khartinger/RCC5V_3d-printable-parts-for-n-scale-modules/images/300_3D_blockpanel_2of3.png

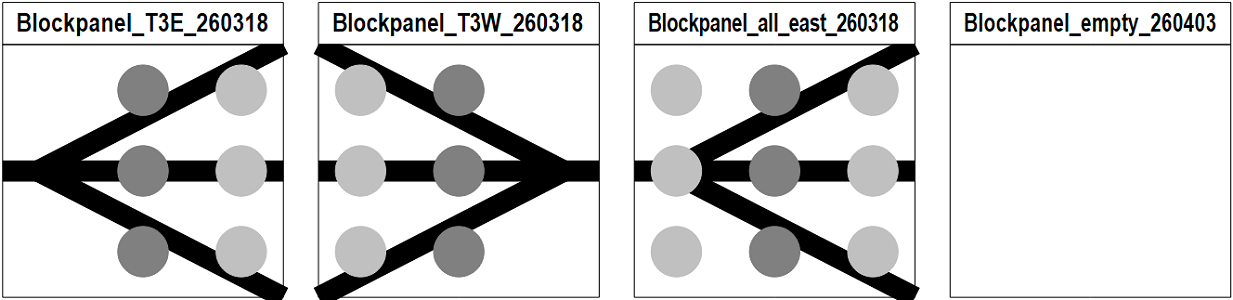
images/300_3D_blockpanel_2of3.png
