khartinger/RCC5V_3d-printable-parts-for-n-scale-modules/images/300_bahnkoerper2.png

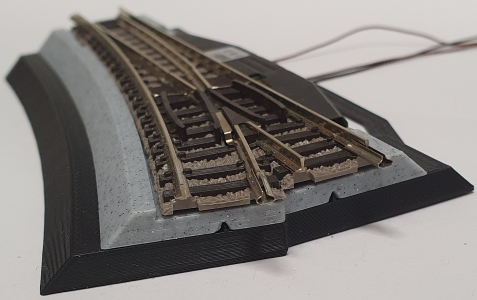
images/300_bahnkoerper2.png
