khartinger/RCC5V_3d-printable-parts-for-n-scale-modules/images/300_pp6_point_motor_cover_t2r_stairs_in.png

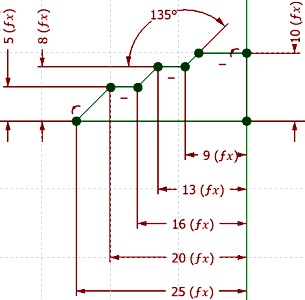
images/300_pp6_point_motor_cover_t2r_stairs_in.png
