khartinger/RCC5V_3d-printable-parts-for-n-scale-modules/images/o_3D_blockpanel_3of3.png

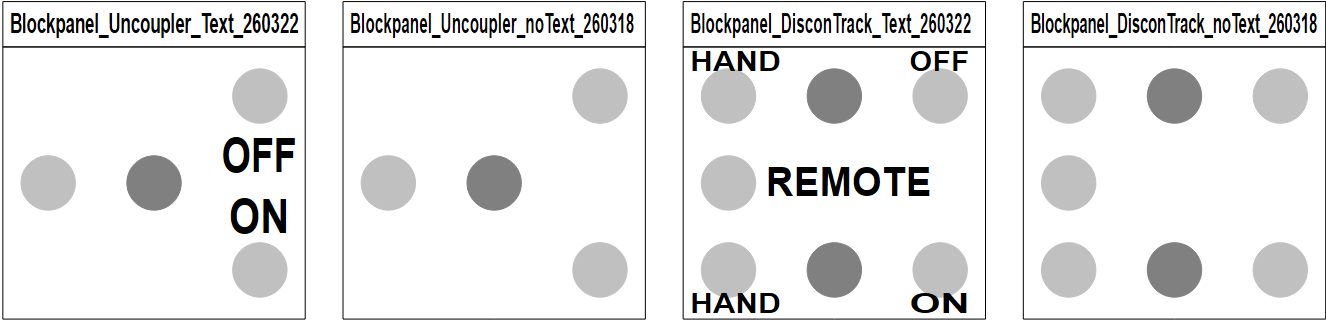
images/o_3D_blockpanel_3of3.png
