khartinger/RCC5V_3d-printable-parts-for-n-scale-modules/fab/pp2_baseboard_frame/3mf/Rahmen_2xFront_S__230mm_260408.3mf

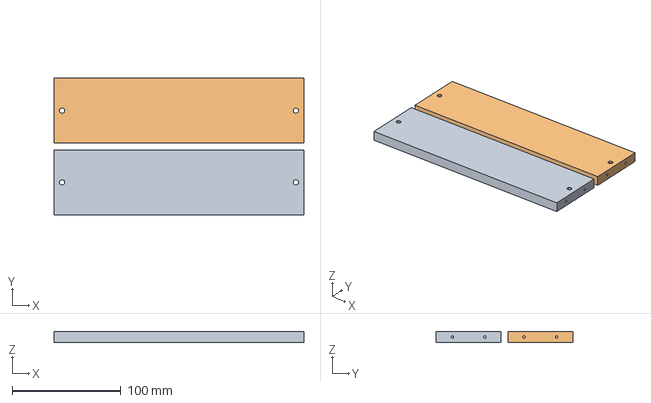
[picture p55: CAD file, 2026-04-10]
fab/pp2_baseboard_frame/3mf/Rahmen_2xFront_S__230mm_260408.3mf
230.0 x 126.0 x 10.0 mm
Rahmen_Front_S__230mm_260408 x 2
