khartinger/RCC5V_3d-printable-parts-for-n-scale-modules/fab/pp2_baseboard_frame/fcstd/Rahmen_Front_S__230mm_260408.FCStd

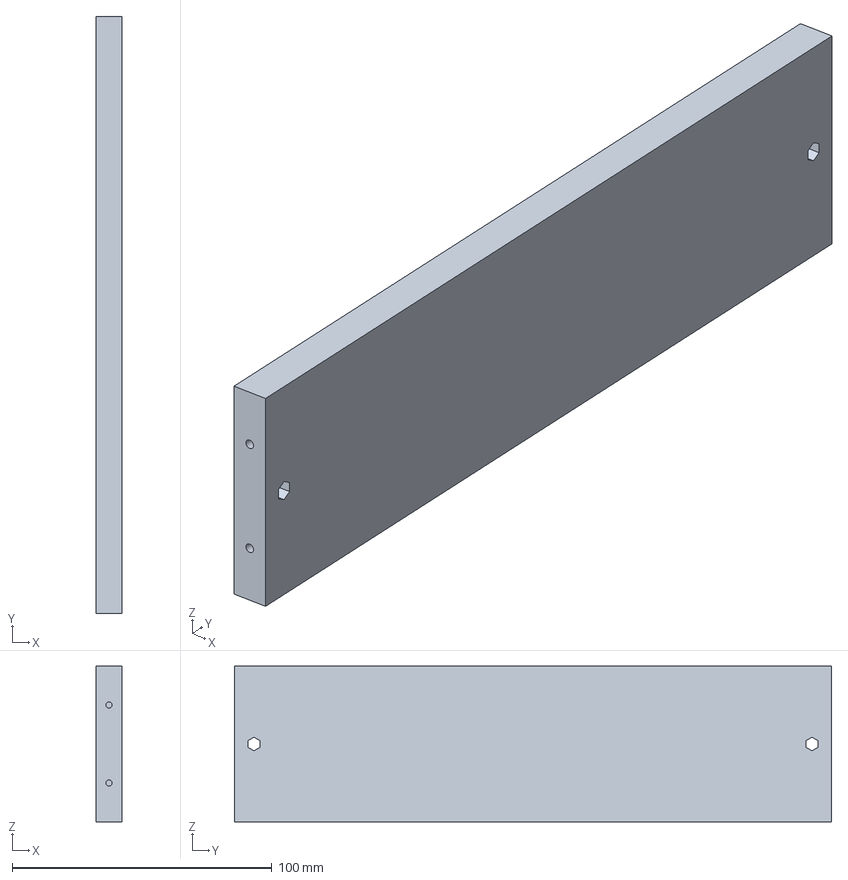
[picture p56: CAD file, 2026-04-10]
fab/pp2_baseboard_frame/fcstd/Rahmen_Front_S__230mm_260408.FCStd
10.0 x 230.0 x 60.0 mm
