khartinger/RCC5V_3d-printable-parts-for-n-scale-modules/fab/pp3_block_panel/3mf/Blockpanel_empty_prusa_260403.3mf

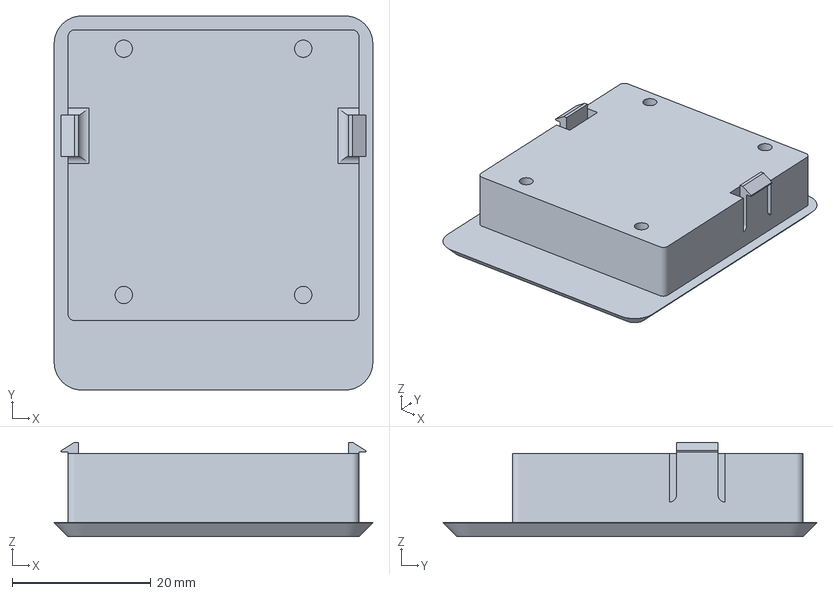
[picture p57: CAD file, 2026-04-10]
fab/pp3_block_panel/3mf/Blockpanel_empty_prusa_260403.3mf
46.0 x 54.0 x 13.6 mm
