khartinger/RCC5V_3d-printable-parts-for-n-scale-modules/fab/pp3_block_panel/fcstd/Blockpanel_DisconTrack_Text_260322.FCStd

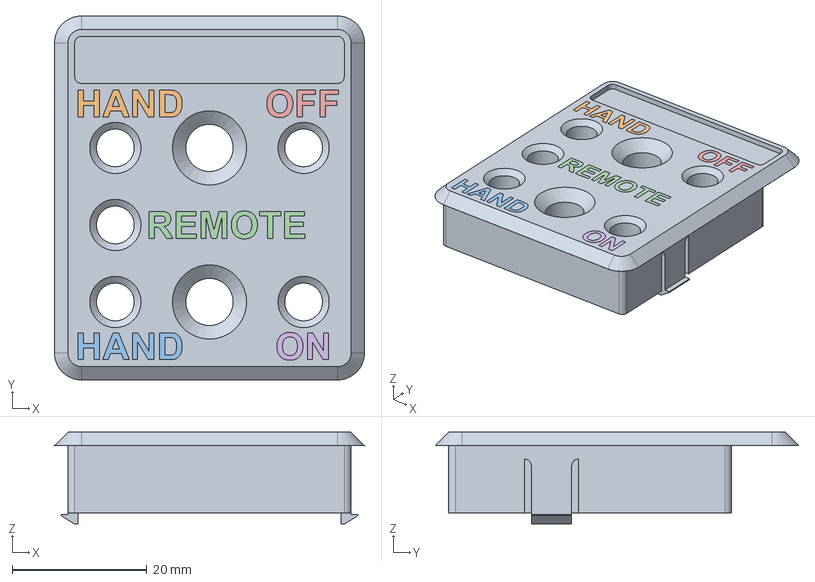
[picture p59: CAD file, 2026-04-05]
fab/pp3_block_panel/fcstd/Blockpanel_DisconTrack_Text_260322.FCStd
46.0 x 54.0 x 13.6 mm
KörperBlock
Extrude_HAND1
Extrude_HAND2
Extrude_REM
Extrude_OFF
Extrude_ON
