khartinger/RCC5V_3d-printable-parts-for-n-scale-modules/fab/pp4_track_ballast/fcstd/Bogen_Schotter_R2_7.5_9128_260327.FCStd

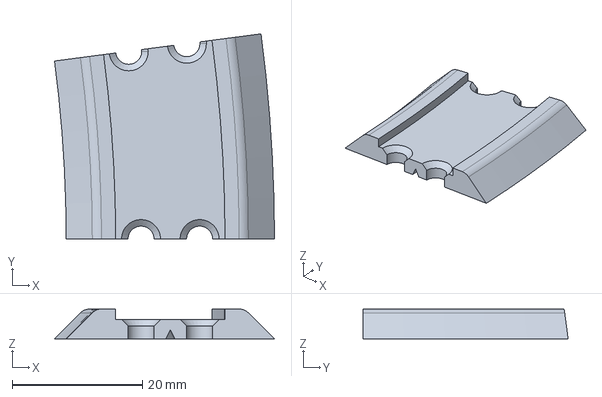
[picture p60: CAD file, 2026-04-17]
fab/pp4_track_ballast/fcstd/Bogen_Schotter_R2_7.5_9128_260327.FCStd
33.8 x 31.5 x 4.60 mm
