khartinger/RCC5V_3d-printable-parts-for-n-scale-modules/fab/pp6_point_motor_cover/fcstd/point_motor_cover_t3r_high_260413.FCStd

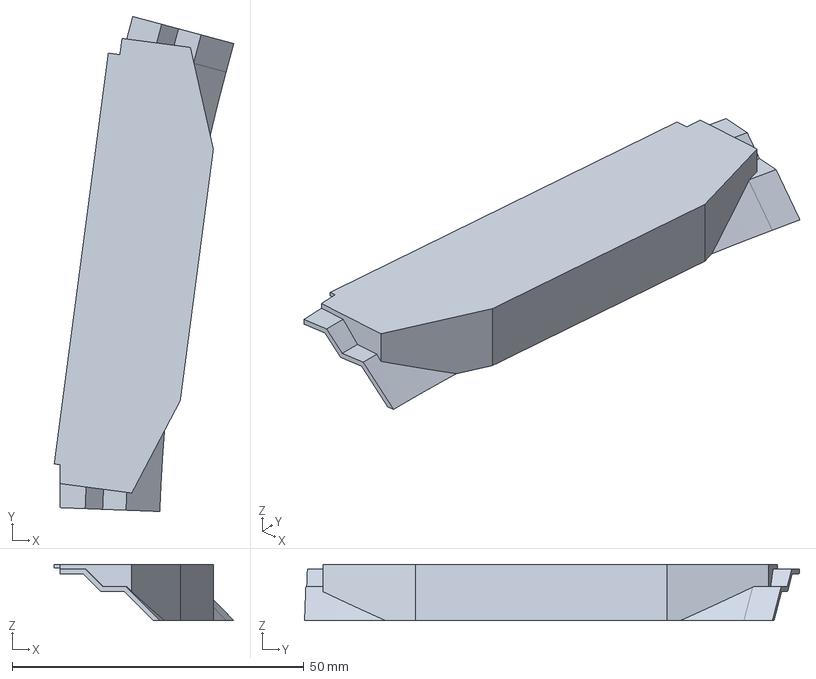
[picture p61: CAD file, 2026-04-13]
fab/pp6_point_motor_cover/fcstd/point_motor_cover_t3r_high_260413.FCStd
30.8 x 84.8 x 9.60 mm
