khartinger/RCC5V_3d-printable-parts-for-n-scale-modules/fab/pp7_tools/fcstd/drill_template_T2_260413.FCStd

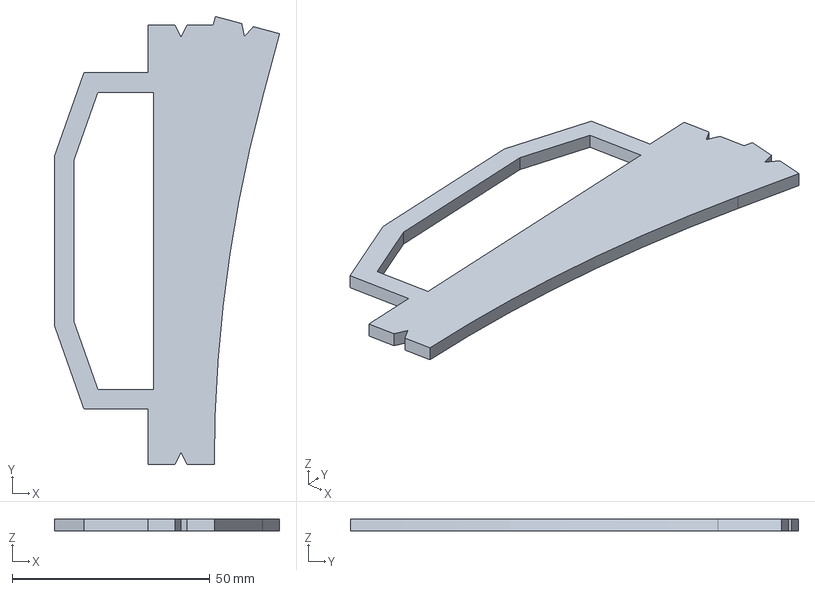
[picture p62: CAD file, 2026-04-13]
fab/pp7_tools/fcstd/drill_template_T2_260413.FCStd
56.9 x 113.2 x 3.00 mm
