khartinger/RCC5V_3d-printable-parts-for-n-scale-modules/fab/pp7_tools/raaco_lid/3mf/Raacodeckel_A9-2_5x_PETG_260427.3mf

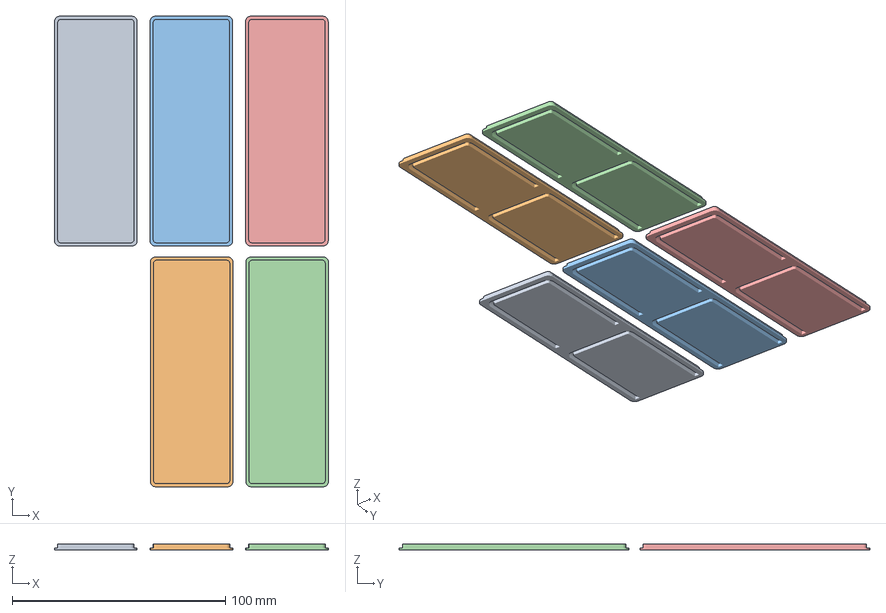
[picture p63: CAD file, 2026-04-29]
fab/pp7_tools/raaco_lid/3mf/Raacodeckel_A9-2_5x_PETG_260427.3mf
128.5 x 220.7 x 3.00 mm
Raacodeckel_A9-2_c_260414 x 5
