khartinger/RCC5V_3d-printable-parts-for-n-scale-modules/fab/pp7_tools/raaco_lid/fcstd/Raacodeckel_A8-1_260415.FCStd

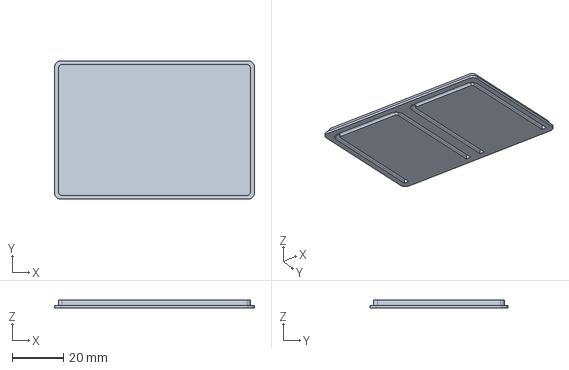
[picture p64: CAD file, 2026-04-15]
fab/pp7_tools/raaco_lid/fcstd/Raacodeckel_A8-1_260415.FCStd
78.0 x 54.0 x 3.00 mm
