khartinger/RCC5V_3d-printable-parts-for-n-scale-modules/fab/pp8_supplement/3mf/suppl_strightcurvedR3_E8_15deg_260429.3mf

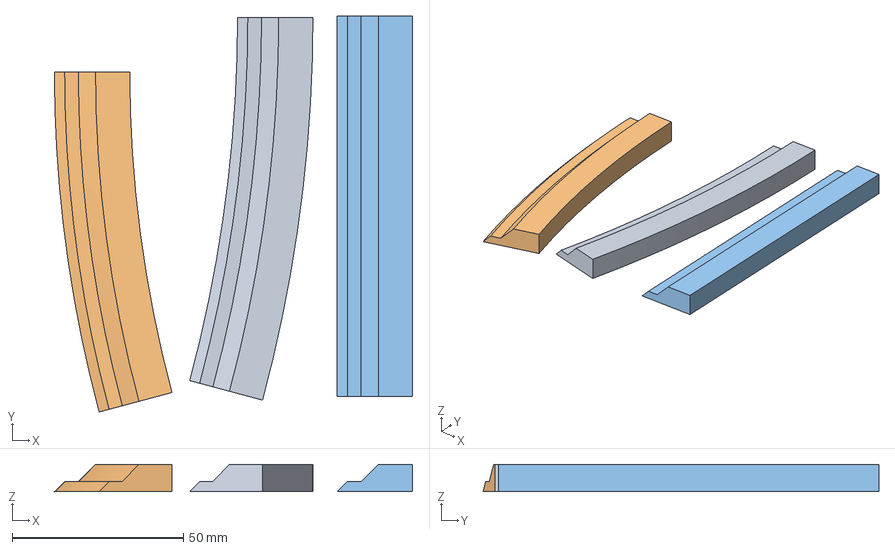
[picture p65: CAD file, 2026-04-30]
fab/pp8_supplement/3mf/suppl_strightcurvedR3_E8_15deg_260429.3mf
104.5 x 115.5 x 8.00 mm
suppl_curvedR3out_E8_15deg_260429
suppl_curvedR3in_E8_15deg_260429
suppl_straight_E8_111mm_260429
