khartinger/RCC5V_3d-printable-parts-for-n-scale-modules/fab/pp9_projects/ReflectiveOptocoupler/3mf/Opto_Beilage_alle_260531.3mf

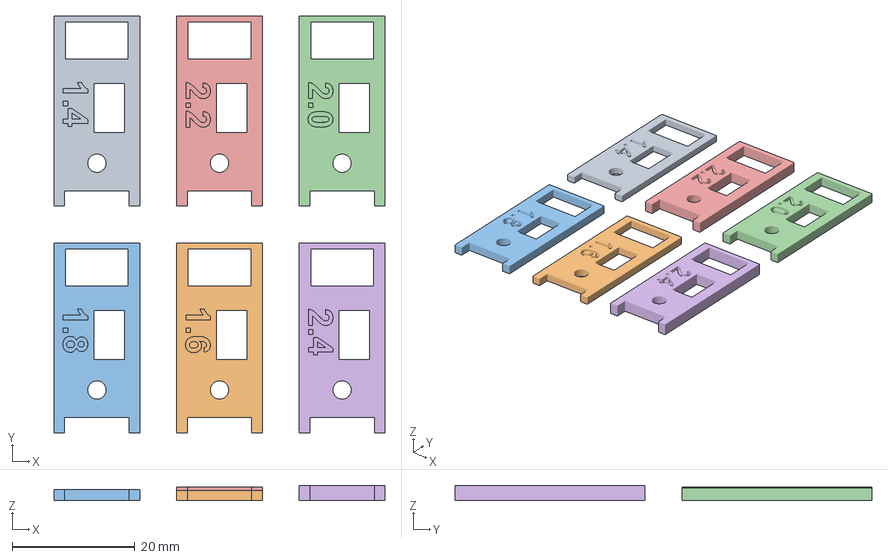
[picture p67: CAD file, 2026-06-02]
fab/pp9_projects/ReflectiveOptocoupler/3mf/Opto_Beilage_alle_260531.3mf
54.0 x 68.0 x 2.40 mm
Opto_Beilage_1.4mm_260531
Opto_Beilage_1.6mm_260531
Opto_Beilage_1.8mm_260531
Opto_Beilage_2.0mm_260531
Opto_Beilage_2.2mm_260531
Opto_Beilage_2.4mm_260531
