khartinger/RCC5V_3d-printable-parts-for-n-scale-modules/fab/pp9_projects/ReflectiveOptocoupler/fcstd/Gerade_Schotter_9103_Opto_b_260531.FCStd

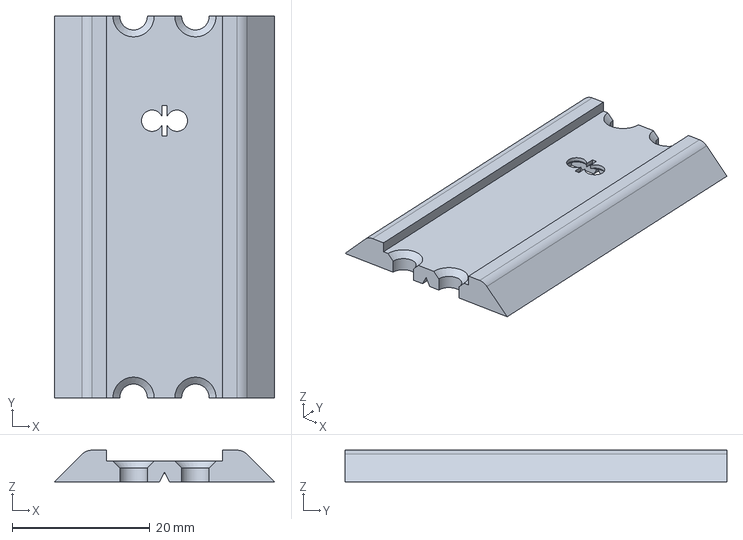
[picture p68: CAD file, 2026-06-02]
fab/pp9_projects/ReflectiveOptocoupler/fcstd/Gerade_Schotter_9103_Opto_b_260531.FCStd
32.0 x 55.5 x 4.60 mm
