khartinger/RCC5V_3d-printable-parts-for-n-scale-modules/fab/pp2_baseboard_frame/3mf/Rahmen_2xSeiteEingleisig_260312.3mf

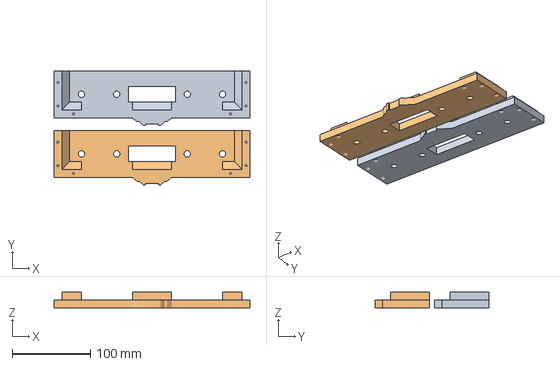
[picture p69: CAD file, 2026-04-10]
fab/pp2_baseboard_frame/3mf/Rahmen_2xSeiteEingleisig_260312.3mf
250.0 x 146.0 x 20.0 mm
Rahmen_SeiteEingleisig_260312 x 2
