khartinger/RCC5V_3d-printable-parts-for-n-scale-modules/fab/pp2_baseboard_frame/fcstd/Rahmen_SeiteEingleisig_260312.FCStd

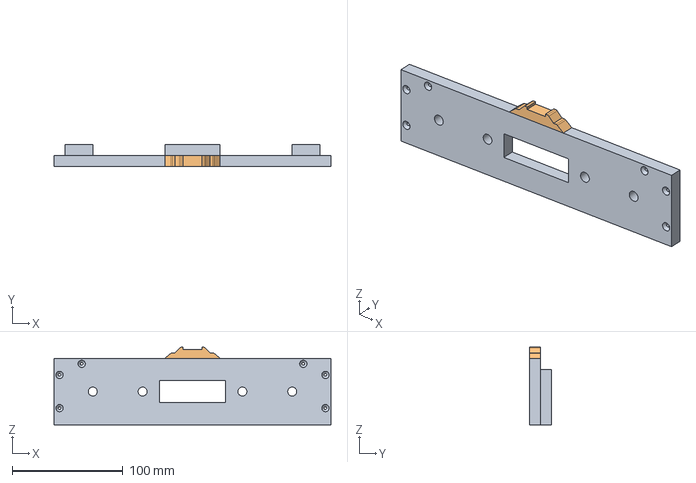
[picture p70: CAD file, 2026-04-06]
fab/pp2_baseboard_frame/fcstd/Rahmen_SeiteEingleisig_260312.FCStd
250.0 x 20.0 x 70.0 mm
KörperRahmen
Körper1Gleis
