khartinger/RCC5V_3d-printable-parts-for-n-scale-modules/fab/pp3_block_panel/3mf/Blockpanel_4x_empty_prusa_260404.3mf

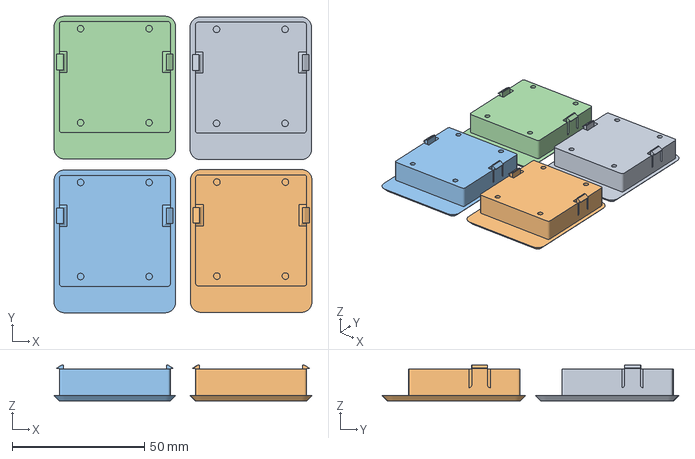
[picture p71: CAD file, 2026-04-10]
fab/pp3_block_panel/3mf/Blockpanel_4x_empty_prusa_260404.3mf
97.6 x 112.2 x 13.6 mm
Blockpanel_empty_260403 x 4
