khartinger/RCC5V_3d-printable-parts-for-n-scale-modules/fab/pp6_point_motor_cover/3mf/point_motor_cover_t2_E8_pair_260413.3mf

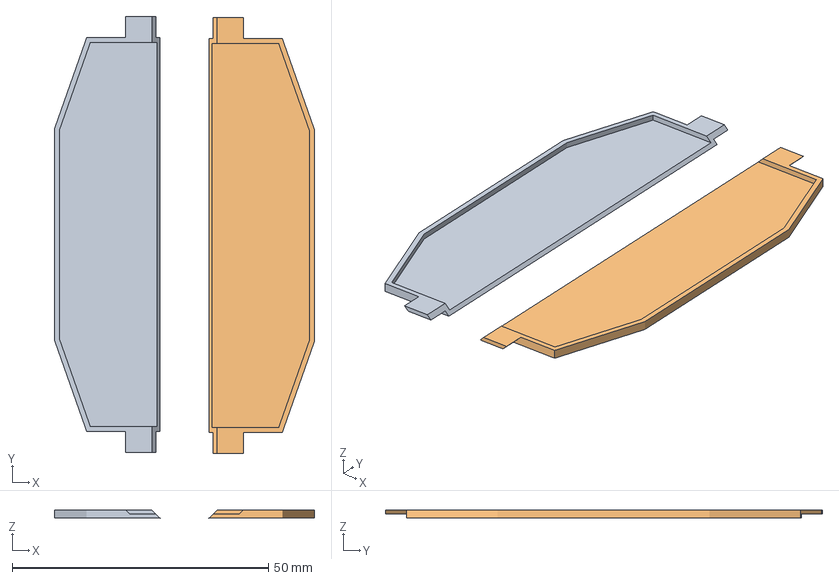
[picture p75: CAD file, 2026-04-13]
fab/pp6_point_motor_cover/3mf/point_motor_cover_t2_E8_pair_260413.3mf
50.8 x 85.4 x 1.60 mm
point_motor_cover_t2r_E8_260413 x 2
