khartinger/RCC5V_3d-printable-parts-for-n-scale-modules/fab/pp6_point_motor_cover/fcstd/point_motor_cover_t2r_E8_260413.FCStd

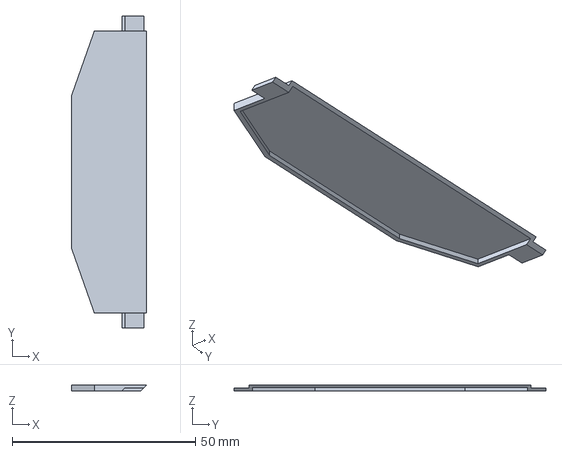
[picture p76: CAD file, 2026-04-13]
fab/pp6_point_motor_cover/fcstd/point_motor_cover_t2r_E8_260413.FCStd
20.6 x 85.2 x 1.60 mm
