khartinger/RCC5V_3d-printable-parts-for-n-scale-modules/fab/pp7_tools/fcstd/drill_template_T3_260413.FCStd

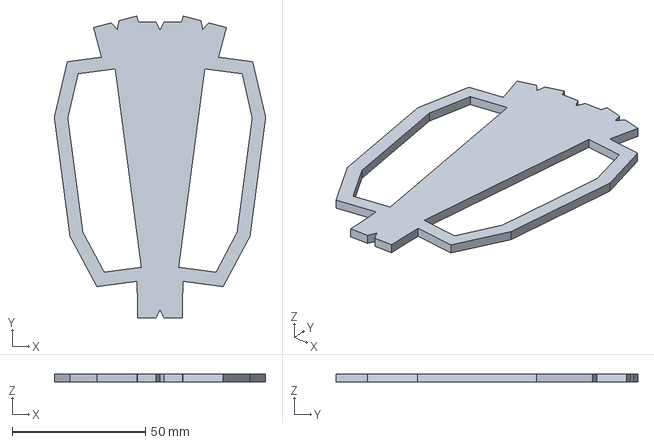
[picture p77: CAD file, 2026-04-13]
fab/pp7_tools/fcstd/drill_template_T3_260413.FCStd
79.2 x 113.2 x 3.00 mm
