khartinger/RCC5V_3d-printable-parts-for-n-scale-modules/fab/pp2_baseboard_frame/3mf/Rahmen_Front_W__240mm_prusa_260406.3mf

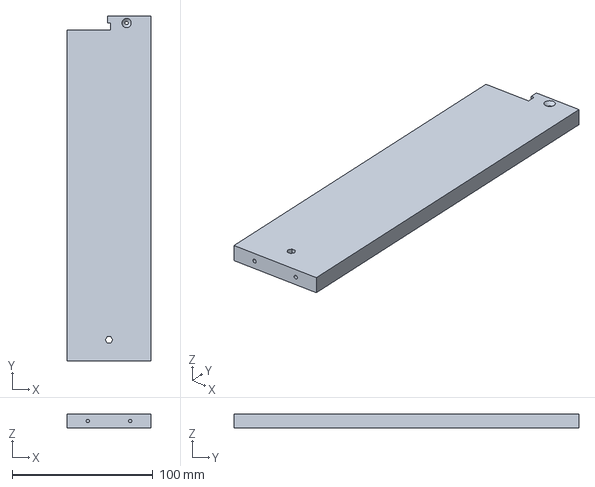
[picture p80: CAD file, 2026-04-06]
fab/pp2_baseboard_frame/3mf/Rahmen_Front_W__240mm_prusa_260406.3mf
60.0 x 245.0 x 10.0 mm
