khartinger/RCC5V_3d-printable-parts-for-n-scale-modules/fab/pp2_baseboard_frame/fcstd/Rahmen_Front_S__250mm_260406.FCStd

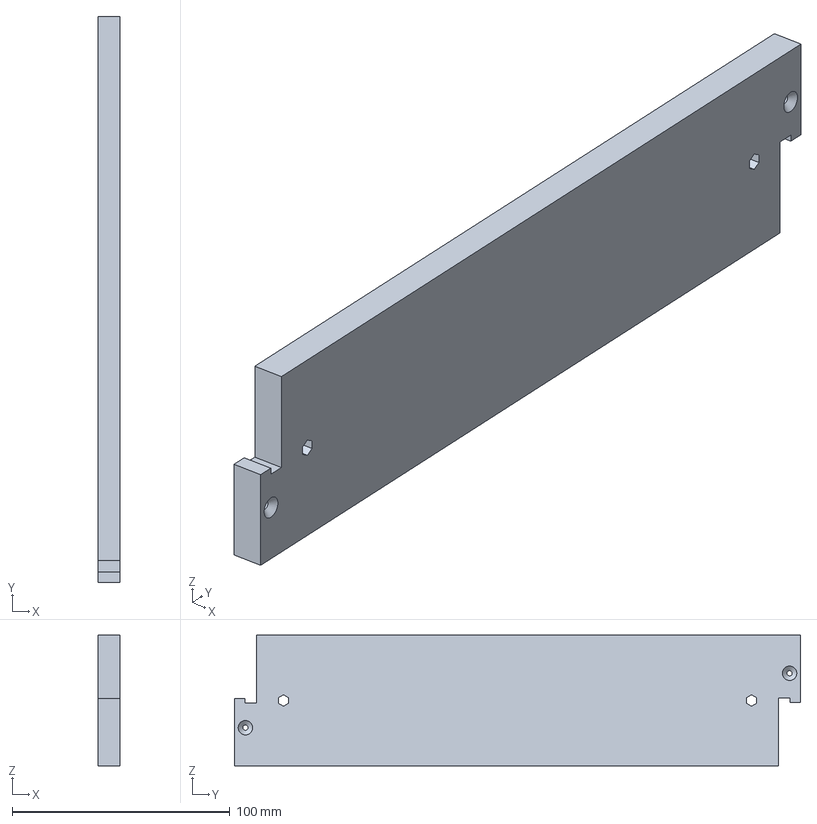
[picture p81: CAD file, 2026-04-06]
fab/pp2_baseboard_frame/fcstd/Rahmen_Front_S__250mm_260406.FCStd
10.0 x 260.0 x 60.0 mm
