khartinger/RCC5V_3d-printable-parts-for-n-scale-modules/fab/pp3_block_panel/3mf/Block_alles_260314.3mf

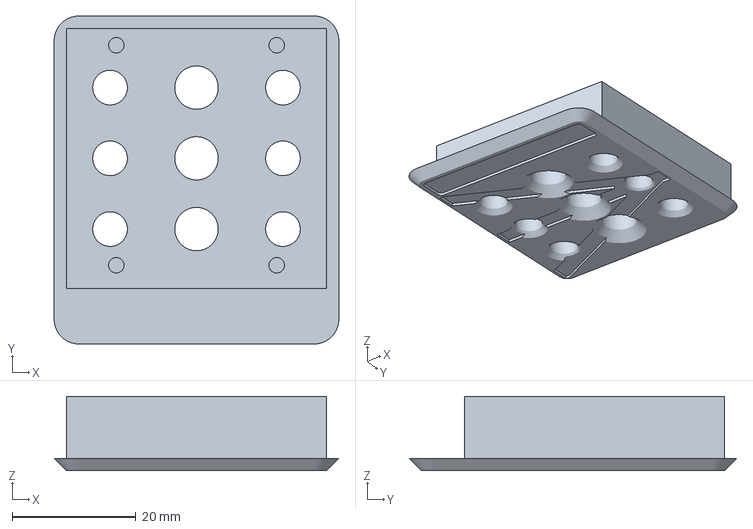
[picture p82: CAD file, 2026-04-10]
fab/pp3_block_panel/3mf/Block_alles_260314.3mf
46.0 x 53.0 x 12.0 mm
