khartinger/RCC5V_3d-printable-parts-for-n-scale-modules/fab/pp4_track_ballast/fcstd/Gerade_Schotter_9101_-10mm_260403.FCStd

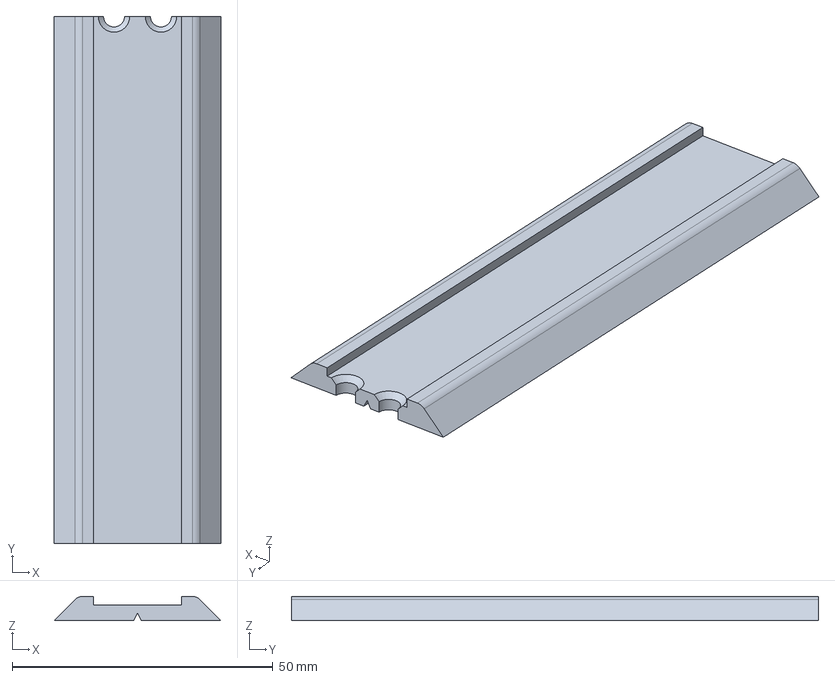
[picture p84: CAD file, 2026-04-17]
fab/pp4_track_ballast/fcstd/Gerade_Schotter_9101_-10mm_260403.FCStd
32.0 x 101.0 x 4.60 mm
