khartinger/RCC5V_3d-printable-parts-for-n-scale-modules/fab/pp5_embankment/fcstd/Gerade_Damm_9100_260429.FCStd

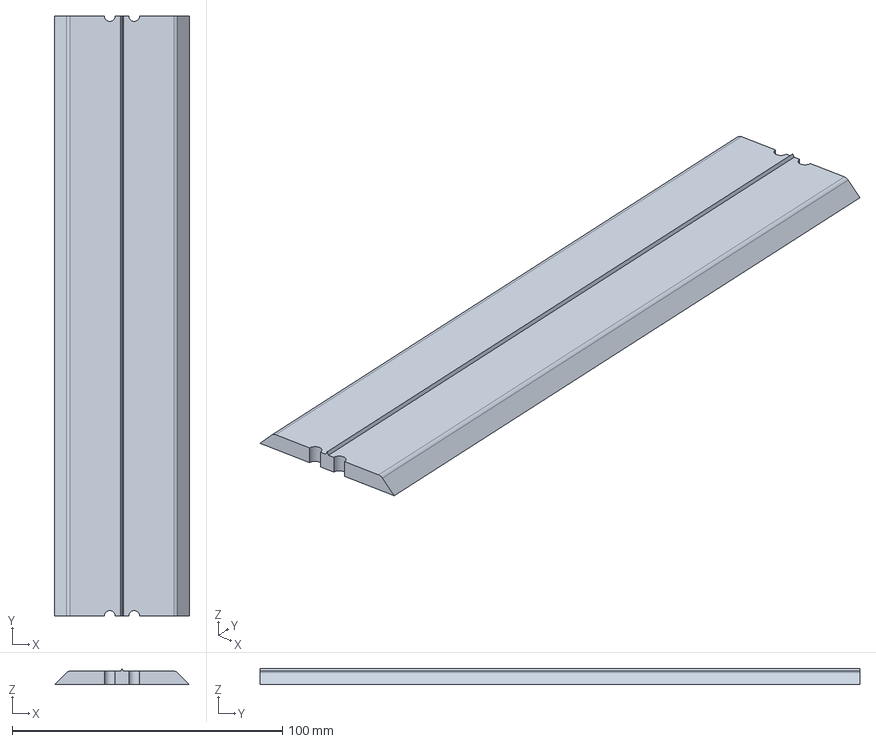
[picture p85: CAD file, 2026-04-29]
fab/pp5_embankment/fcstd/Gerade_Damm_9100_260429.FCStd
50.0 x 222.0 x 6.00 mm
