khartinger/RCC5V_3d-printable-parts-for-n-scale-modules/fab/pp6_point_motor_cover/3mf/point_motor_cover_t3_E8_pair_260413.3mf

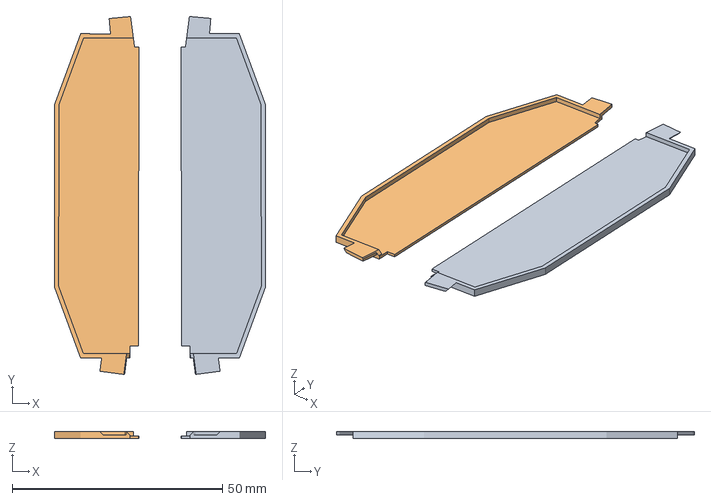
[picture p86: CAD file, 2026-04-13]
fab/pp6_point_motor_cover/3mf/point_motor_cover_t3_E8_pair_260413.3mf
50.1 x 85.1 x 1.60 mm
point_motor_cover_t3r_E8_260413 x 2
