khartinger/RCC5V_3d-printable-parts-for-n-scale-modules/fab/pp6_point_motor_cover/fcstd/point_motor_cover_t2r_high_260413.FCStd

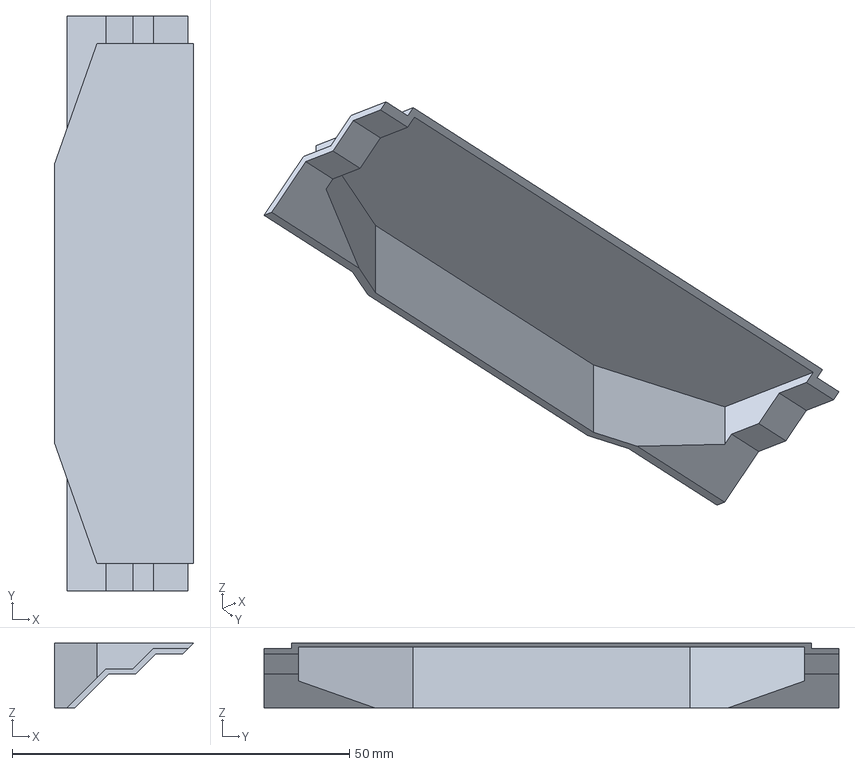
[picture p87: CAD file, 2026-04-13]
fab/pp6_point_motor_cover/fcstd/point_motor_cover_t2r_high_260413.FCStd
20.6 x 85.2 x 9.60 mm
