khartinger/RCC5V_3d-printable-parts-for-n-scale-modules/fab/pp8_supplement/fcstd/suppl_curvedR3out_E8_15deg_260429.FCStd

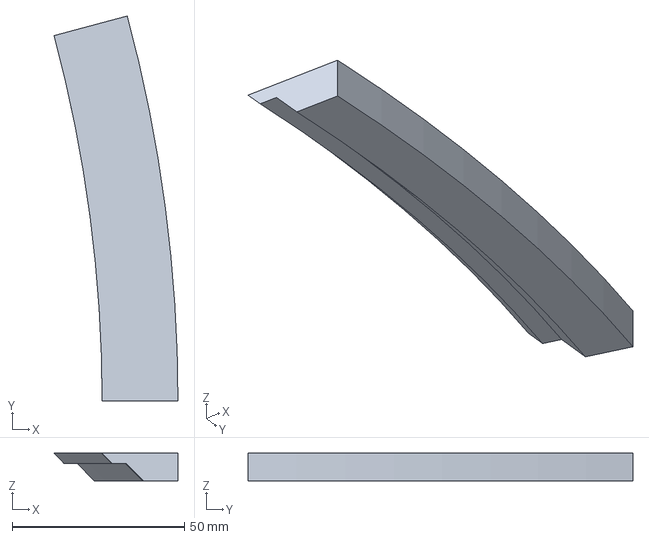
[picture p88: CAD file, 2026-04-30]
fab/pp8_supplement/fcstd/suppl_curvedR3out_E8_15deg_260429.FCStd
35.9 x 111.7 x 8.00 mm
