khartinger/RCC5V_3d-printable-parts-for-n-scale-modules/fab/pp9_projects/ReflectiveOptocoupler/fcstd/Optobohrlehre_9103_260527.FCStd

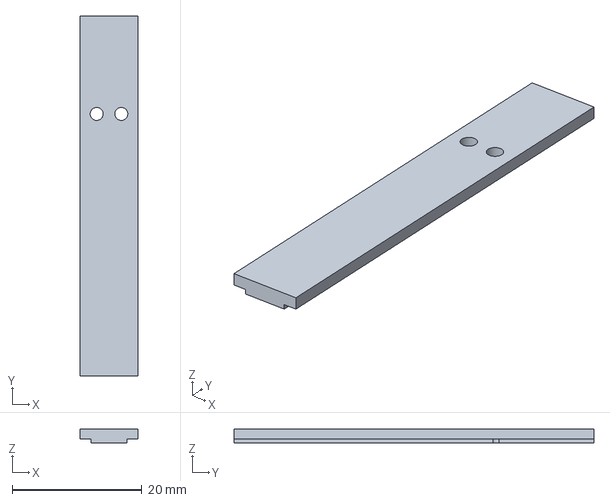
[picture p89: CAD file, 2026-06-02]
fab/pp9_projects/ReflectiveOptocoupler/fcstd/Optobohrlehre_9103_260527.FCStd
9.00 x 55.5 x 2.10 mm
