khartinger/RCC5V_3d-printable-parts-for-n-scale-modules/fab/pp4_track_ballast/fcstd/Weiche3_Schotter_260409.FCStd

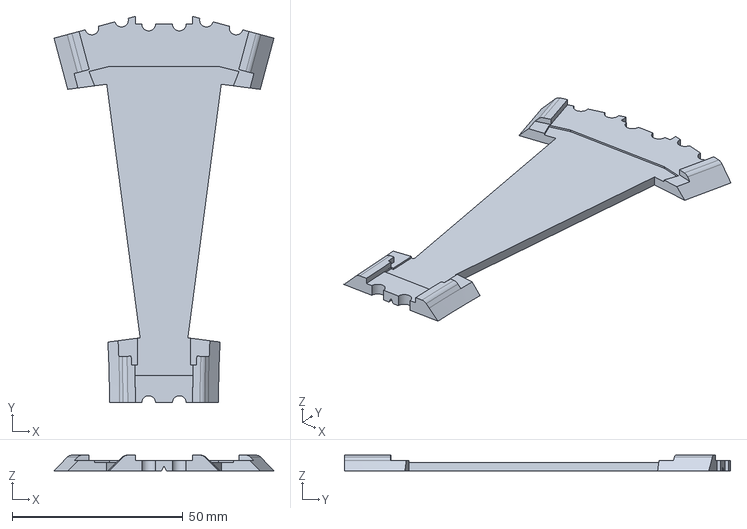
[picture p92: CAD file, 2026-04-10]
fab/pp4_track_ballast/fcstd/Weiche3_Schotter_260409.FCStd
64.5 x 113.3 x 4.60 mm
