khartinger/RCC5V_3d-printable-parts-for-n-scale-modules/fab/pp5_embankment/fcstd/Weiche3_Damm_260409.FCStd

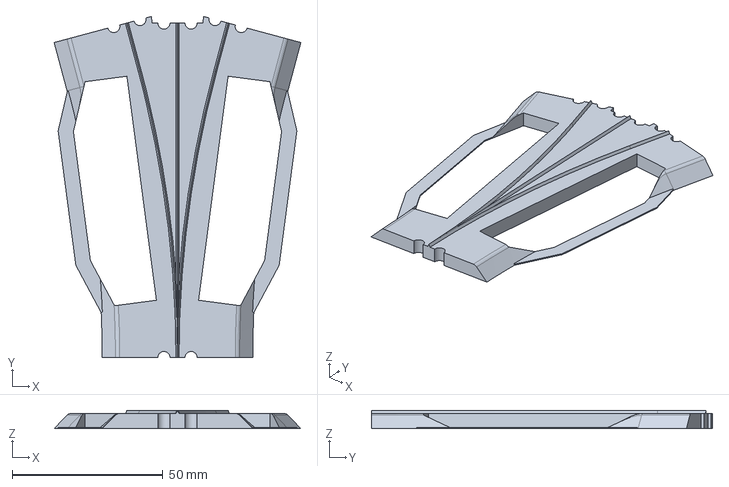
[picture p93: CAD file, 2026-04-13]
fab/pp5_embankment/fcstd/Weiche3_Damm_260409.FCStd
81.9 x 113.2 x 6.00 mm
