khartinger/RCC5V_3d-printable-parts-for-n-scale-modules/fab/pp6_point_motor_cover/3mf/point_motor_cover_t2_high_pair_260413.3mf

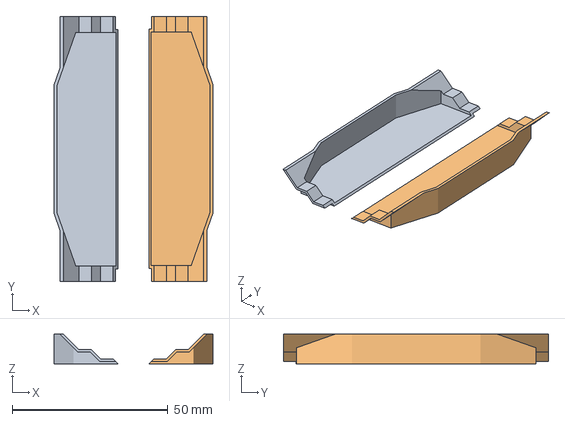
[picture p94: CAD file, 2026-04-13]
fab/pp6_point_motor_cover/3mf/point_motor_cover_t2_high_pair_260413.3mf
51.1 x 85.3 x 9.60 mm
point_motor_cover_t2r_high_260413 x 2
