khartinger/RCC5V_3d-printable-parts-for-n-scale-modules/fab/pp7_tools/raaco_lid/3mf/Raacodeckel_A9-2_5x_260414.3mf

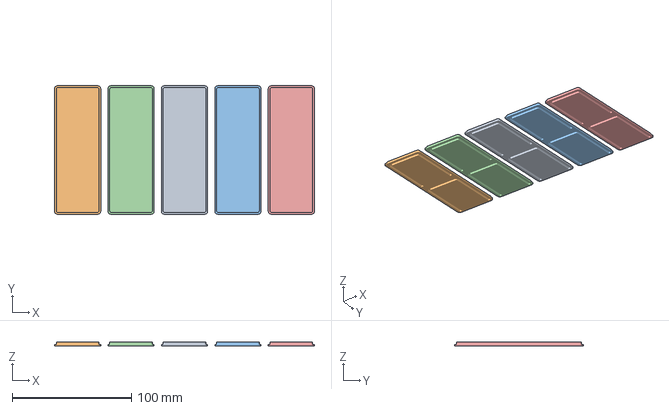
[picture p95: CAD file, 2026-04-15]
fab/pp7_tools/raaco_lid/3mf/Raacodeckel_A9-2_5x_260414.3mf
218.0 x 107.8 x 3.00 mm
Raacodeckel_A9-2_c_260414 x 5
