khartinger/RCC5V_3d-printable-parts-for-n-scale-modules/fab/pp8_supplement/fcstd/suppl_curvedR3out_E8_7.5deg_260429.FCStd

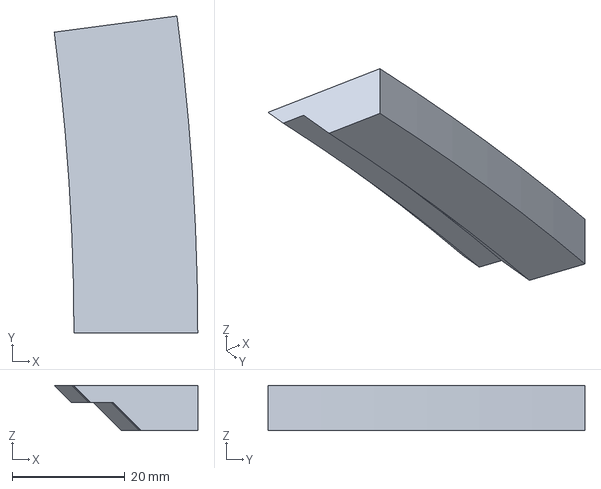
[picture p96: CAD file, 2026-04-30]
fab/pp8_supplement/fcstd/suppl_curvedR3out_E8_7.5deg_260429.FCStd
25.5 x 56.3 x 8.00 mm
