khartinger/RCC5V_3d-printable-parts-for-n-scale-modules/fab/pp2_baseboard_frame/3mf/Rahmen_Front_W_Oled_34_240mm_prusa_260401.3mf

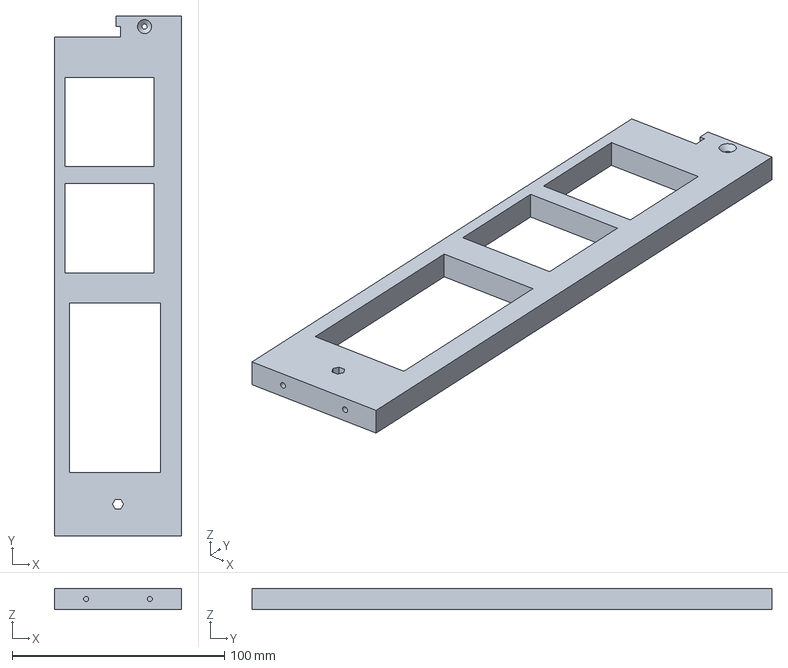
[picture p98: CAD file, 2026-04-06]
fab/pp2_baseboard_frame/3mf/Rahmen_Front_W_Oled_34_240mm_prusa_260401.3mf
60.0 x 245.0 x 10.0 mm
