khartinger/RCC5V_3d-printable-parts-for-n-scale-modules/fab/pp2_baseboard_frame/fcstd/Rahmen_Quer_230mm_260313.FCStd

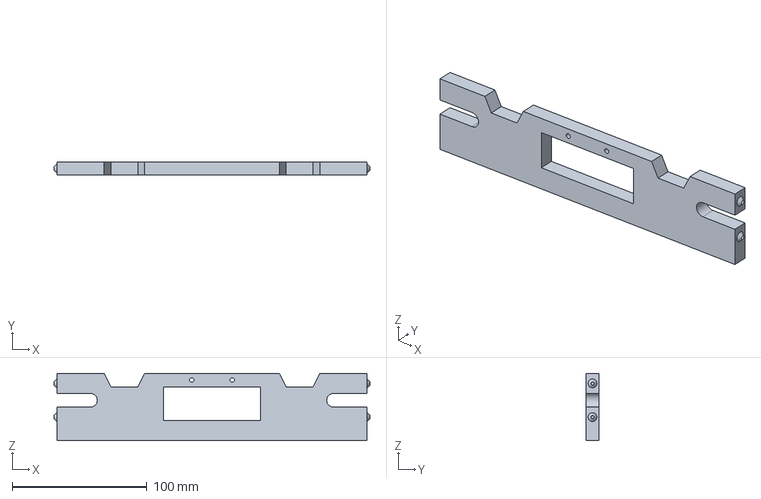
[picture p99: CAD file, 2026-04-06]
fab/pp2_baseboard_frame/fcstd/Rahmen_Quer_230mm_260313.FCStd
234.1 x 10.0 x 50.0 mm
