khartinger/RCC5V_3d-printable-parts-for-n-scale-modules/fab/pp3_block_panel/3mf/6xBlockpanel_prusa_260319.3mf

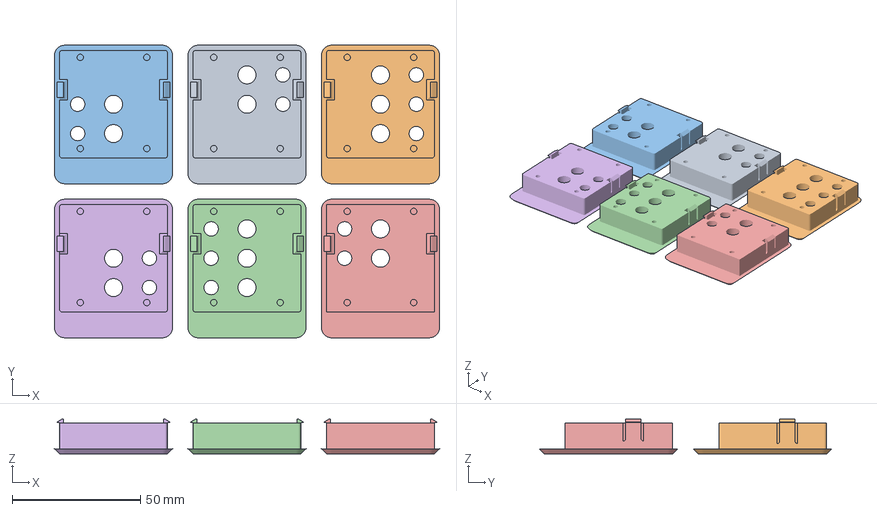
[picture p100: CAD file, 2026-04-10]
fab/pp3_block_panel/3mf/6xBlockpanel_prusa_260319.3mf
150.0 x 114.0 x 13.6 mm
Blockpanel_T2RE_260318
Blockpanel_T3E_260318
Blockpanel_T2RW_260318
Blockpanel_T3W_260318
Blockpanel_T2LW_260318
Blockpanel_T2LE_260318
