khartinger/RCC5V_3d-printable-parts-for-n-scale-modules/fab/pp3_block_panel/fcstd/Blockpanel_all_east_260318.FCStd

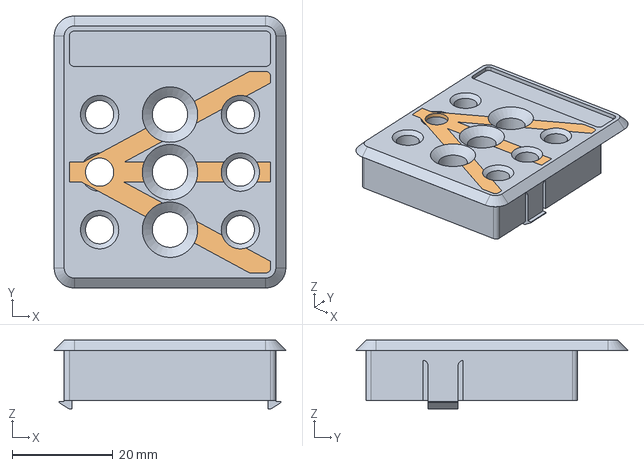
[picture p101: CAD file, 2026-04-05]
fab/pp3_block_panel/fcstd/Blockpanel_all_east_260318.FCStd
46.0 x 54.0 x 13.6 mm
KörperBlock
KörperSymbol
