khartinger/RCC5V_3d-printable-parts-for-n-scale-modules/fab/pp4_track_ballast/fcstd/Gerade_Schotter_Iso_0.5mm_260327.FCStd

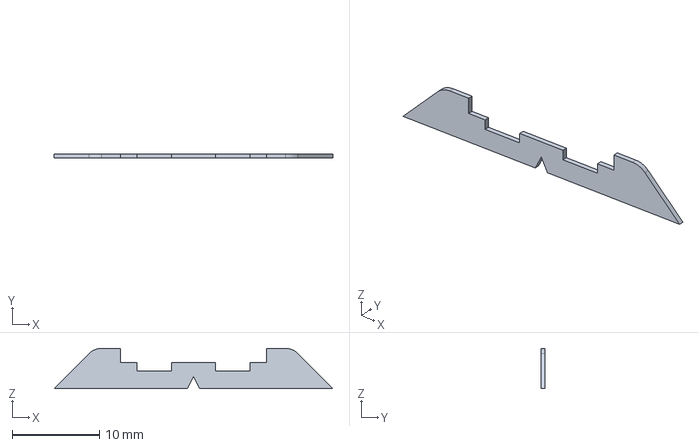
[picture p102: CAD file, 2026-04-10]
fab/pp4_track_ballast/fcstd/Gerade_Schotter_Iso_0.5mm_260327.FCStd
32.0 x 0.5 x 4.60 mm
