khartinger/RCC5V_3d-printable-parts-for-n-scale-modules/fab/pp5_embankment/fcstd/Gerade_Damm_9101_adWeiche_260314.FCStd

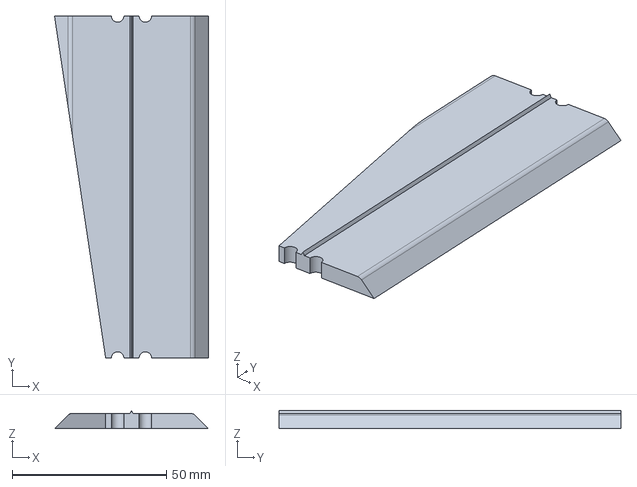
[picture p103: CAD file, 2026-04-10]
fab/pp5_embankment/fcstd/Gerade_Damm_9101_adWeiche_260314.FCStd
50.0 x 111.0 x 6.00 mm
