khartinger/RCC5V_3d-printable-parts-for-n-scale-modules/fab/pp8_supplement/fcstd/suppl_curvedR3in_E8_15deg_260429.FCStd

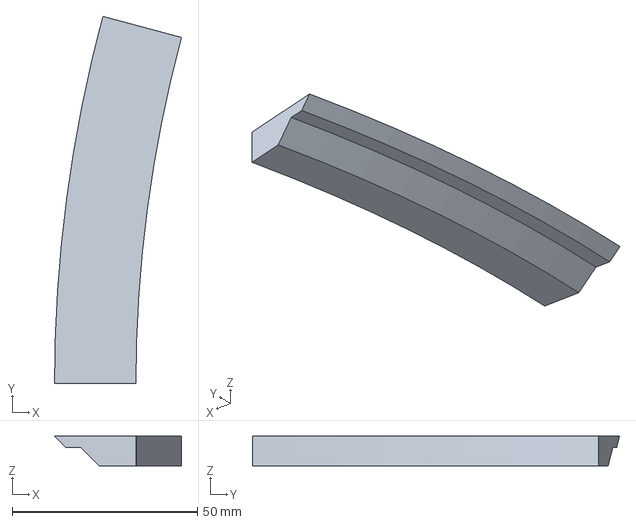
[picture p105: CAD file, 2026-04-30]
fab/pp8_supplement/fcstd/suppl_curvedR3in_E8_15deg_260429.FCStd
34.3 x 99.2 x 8.00 mm
