khartinger/RCC5V_3d-printable-parts-for-n-scale-modules/fab/pp2_baseboard_frame/3mf/Rahmen_4xDistanzplatte_0.8mm_260404.3mf

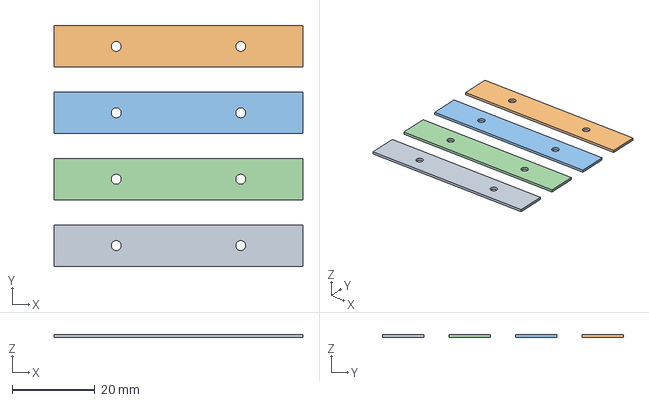
[picture p106: CAD file, 2026-04-06]
fab/pp2_baseboard_frame/3mf/Rahmen_4xDistanzplatte_0.8mm_260404.3mf
60.0 x 58.0 x 0.8 mm
Rahmen_Distanzplatte_0.8mm_260404 x 4
