khartinger/RCC5V_3d-printable-parts-for-n-scale-modules/fab/pp3_block_panel/fcstd/addon/Blockpanel_all_1Koerper_260318.FCStd

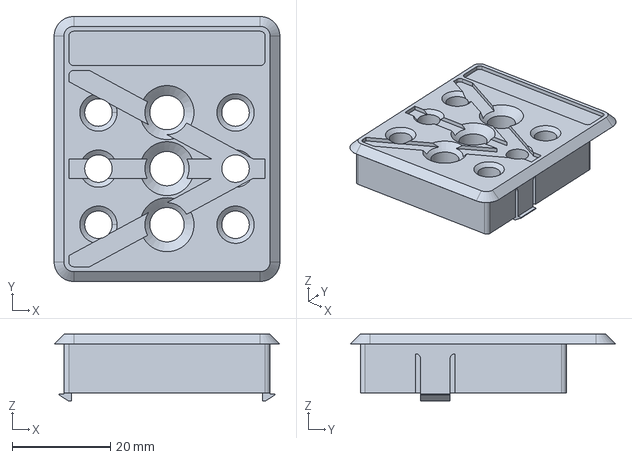
[picture p109: CAD file, 2026-04-05]
fab/pp3_block_panel/fcstd/addon/Blockpanel_all_1Koerper_260318.FCStd
46.0 x 54.0 x 13.6 mm
