khartinger/RCC5V_3d-printable-parts-for-n-scale-modules/fab/pp4_track_ballast/fcstd/Weiche2L_Schotter_parallel_260327.FCStd

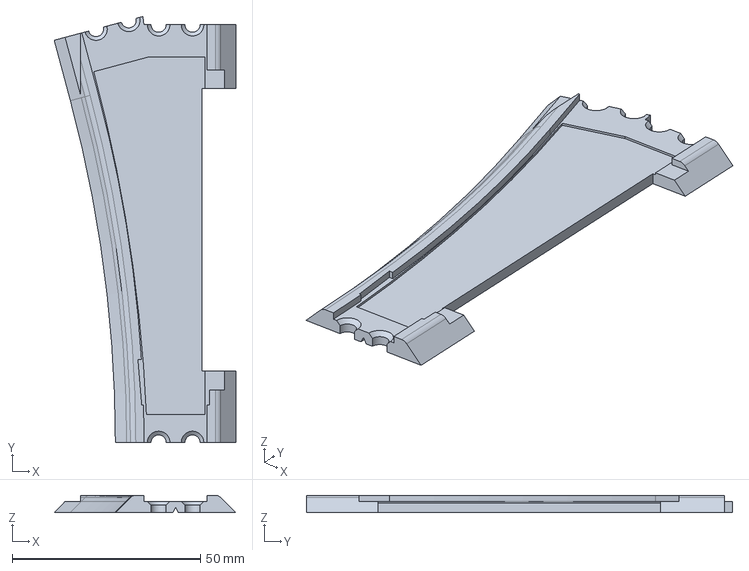
[picture p111: CAD file, 2026-04-10]
fab/pp4_track_ballast/fcstd/Weiche2L_Schotter_parallel_260327.FCStd
48.3 x 113.2 x 4.60 mm
