khartinger/RCC5V_3d-printable-parts-for-n-scale-modules/fab/pp5_embankment/fcstd/Weiche2R_Damm_260314.FCStd

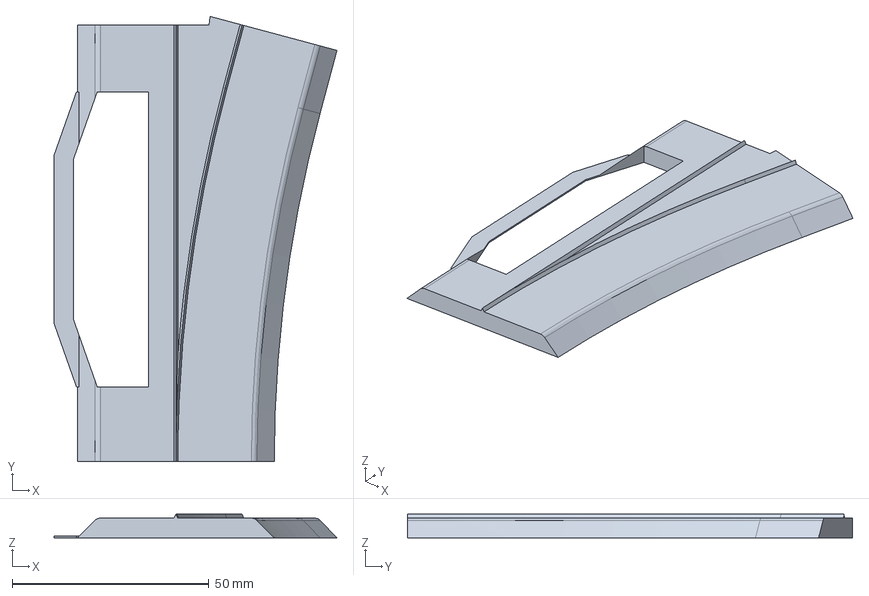
[picture p112: CAD file, 2026-04-10]
fab/pp5_embankment/fcstd/Weiche2R_Damm_260314.FCStd
71.9 x 113.2 x 6.00 mm
