khartinger/RCC5V_3d-printable-parts-for-n-scale-modules/fab/pp8_supplement/fcstd/suppl_straight_E12_50mm_260430.FCStd

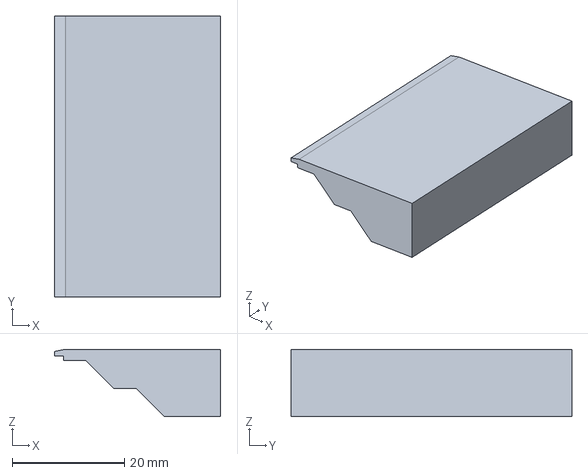
[picture p113: CAD file, 2026-04-30]
fab/pp8_supplement/fcstd/suppl_straight_E12_50mm_260430.FCStd
29.6 x 50.0 x 12.0 mm
