khartinger/RCC5V_3d-printable-parts-for-n-scale-modules/fab/pp2_baseboard_frame/3mf/Rahmen_4xDistanzplatte_1.0mm_260404.3mf

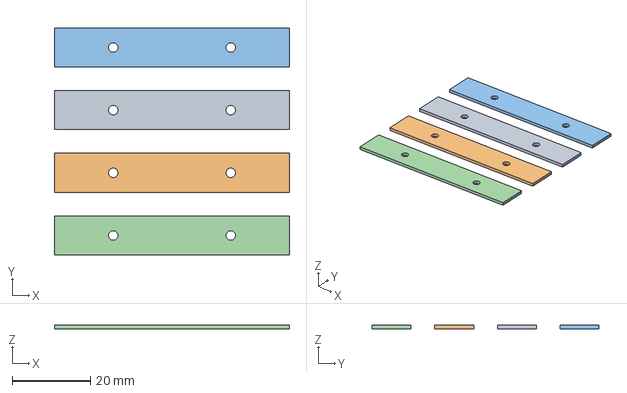
[picture p114: CAD file, 2026-04-06]
fab/pp2_baseboard_frame/3mf/Rahmen_4xDistanzplatte_1.0mm_260404.3mf
60.0 x 58.0 x 1.00 mm
Rahmen_Distanzplatte_1.0mm_260404 x 4
