khartinger/RCC5V_3d-printable-parts-for-n-scale-modules/fab/pp4_track_ballast/fcstd/Bogen_Schotter_R2_45_9125_260327.FCStd

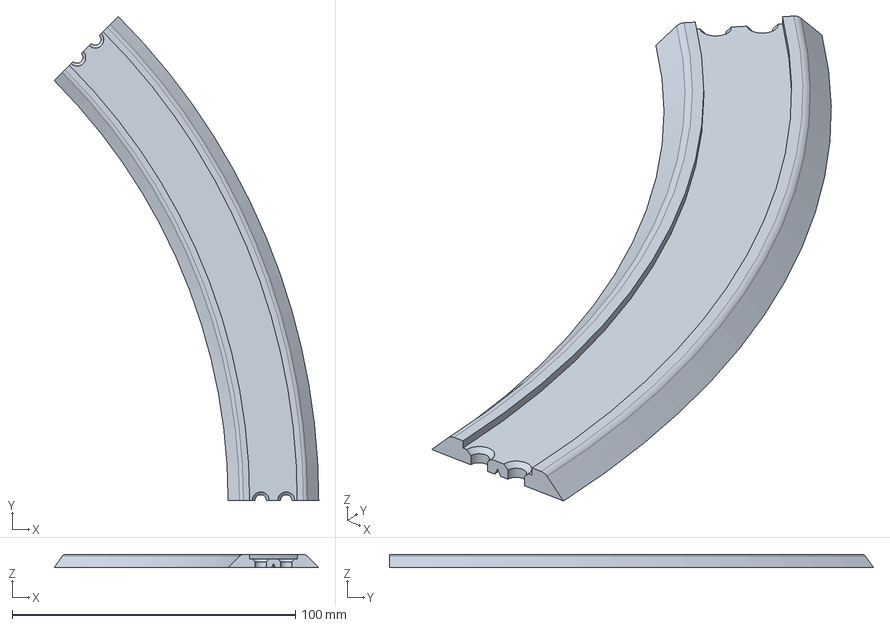
[picture p117: CAD file, 2026-04-10]
fab/pp4_track_ballast/fcstd/Bogen_Schotter_R2_45_9125_260327.FCStd
93.4 x 170.8 x 4.60 mm
