khartinger/RCC5V_3d-printable-parts-for-n-scale-modules/fab/pp5_embankment/fcstd/Gerade_Damm_9103_-10mm_260408.FCStd

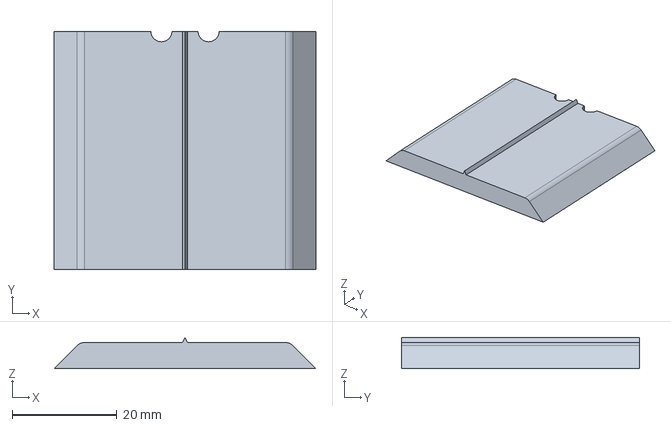
[picture p118: CAD file, 2026-04-10]
fab/pp5_embankment/fcstd/Gerade_Damm_9103_-10mm_260408.FCStd
50.0 x 45.5 x 6.00 mm
