khartinger/RCC5V_3d-printable-parts-for-n-scale-modules/fab/pp8_supplement/fcstd/suppl_straight_E8_XXmm_260429.FCStd

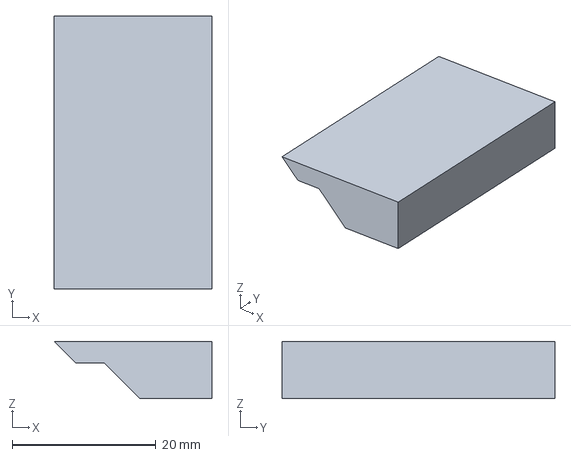
[picture p119: CAD file, 2026-04-30]
fab/pp8_supplement/fcstd/suppl_straight_E8_XXmm_260429.FCStd
22.0 x 38.0 x 8.00 mm
