khartinger/RCC5V_3d-printable-parts-for-n-scale-modules/fab/pp2_baseboard_frame/3mf/Rahmen_Front_SE_12_240mm_260316.3mf

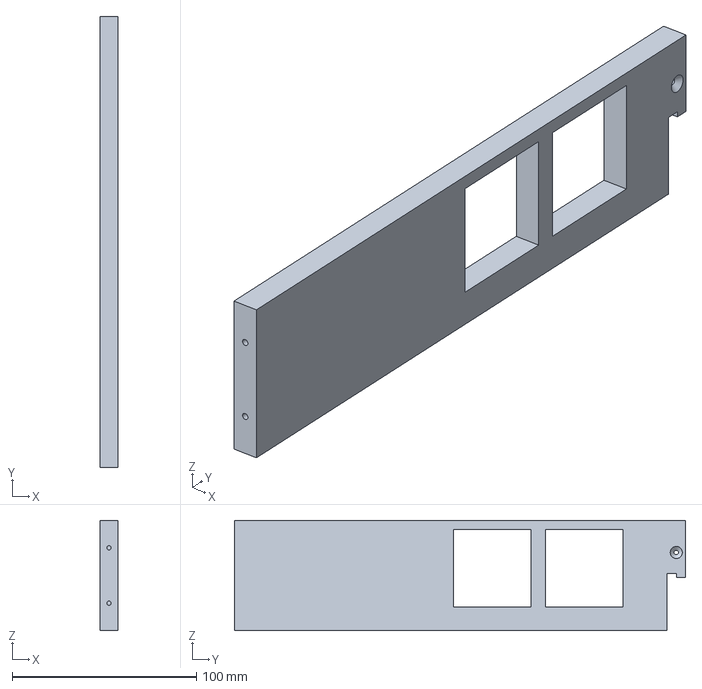
[picture p120: CAD file, 2026-04-06]
fab/pp2_baseboard_frame/3mf/Rahmen_Front_SE_12_240mm_260316.3mf
10.0 x 245.0 x 60.0 mm
