khartinger/RCC5V_3d-printable-parts-for-n-scale-modules/fab/pp5_embankment/fcstd/Bogen_Damm_R3_15_9131_260311.FCStd

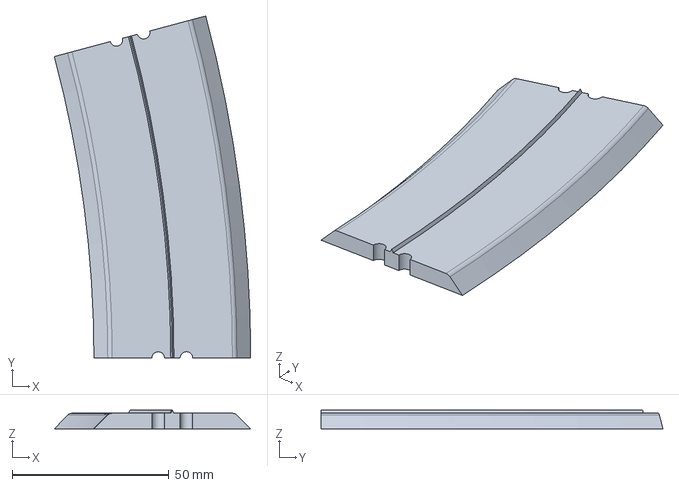
[picture p124: CAD file, 2026-04-10]
fab/pp5_embankment/fcstd/Bogen_Damm_R3_15_9131_260311.FCStd
62.7 x 109.1 x 6.00 mm
