khartinger/RCC5V_3d-printable-parts-for-n-scale-modules/fab/pp2_baseboard_frame/fcstd/Rahmen_Front_S_1234_250mm_260402.FCStd

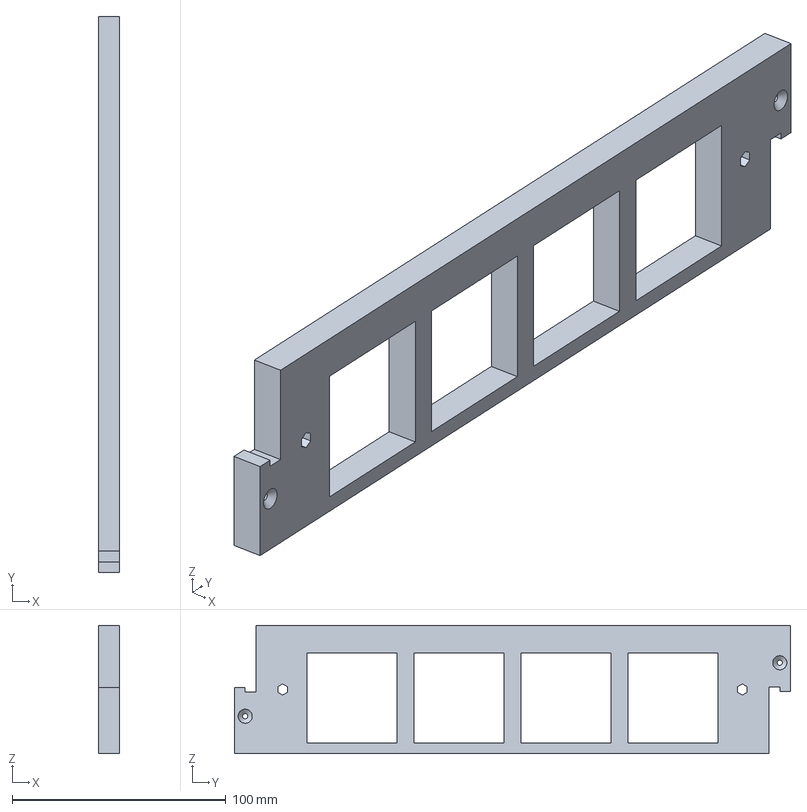
[picture p128: CAD file, 2026-04-05]
fab/pp2_baseboard_frame/fcstd/Rahmen_Front_S_1234_250mm_260402.FCStd
10.0 x 260.0 x 60.0 mm
