khartinger/RCC5V_3d-printable-parts-for-n-scale-modules/fab/pp4_track_ballast/fcstd/Gerade_Schotter_9102_260327.FCStd

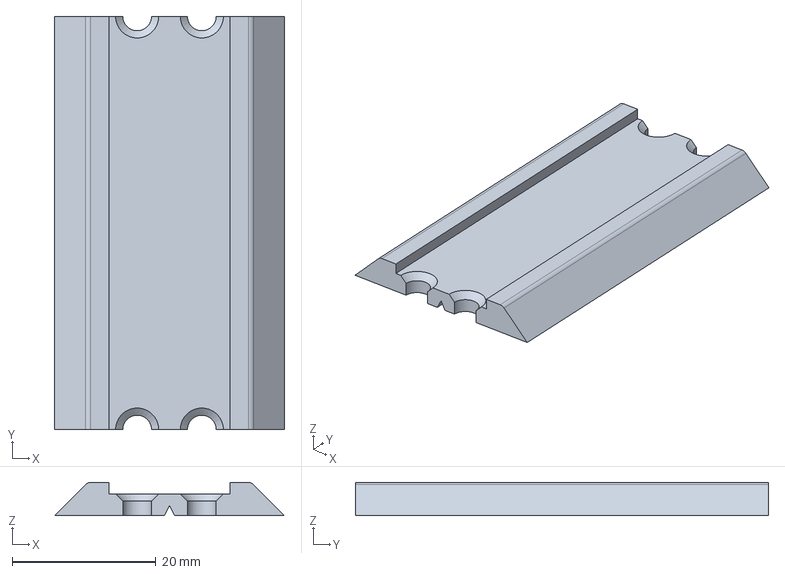
[picture p129: CAD file, 2026-04-10]
fab/pp4_track_ballast/fcstd/Gerade_Schotter_9102_260327.FCStd
32.0 x 57.5 x 4.60 mm
