khartinger/RCC5V_3d-printable-parts-for-n-scale-modules/fab/pp5_embankment/fcstd/Gerade_Damm_Abschluss_260311.FCStd

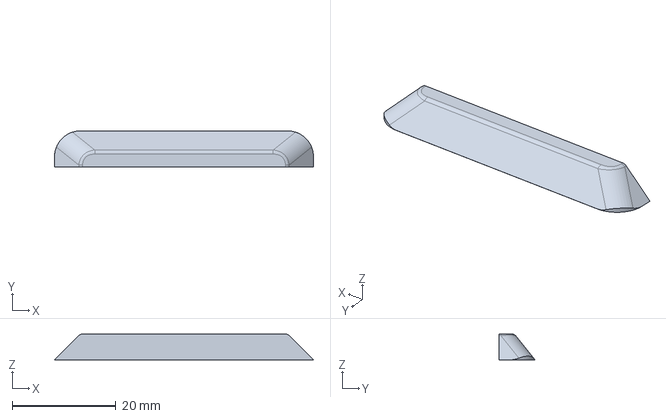
[picture p130: CAD file, 2026-04-10]
fab/pp5_embankment/fcstd/Gerade_Damm_Abschluss_260311.FCStd
50.0 x 7.00 x 5.00 mm
