khartinger/RCC5V_3d-printable-parts-for-n-scale-modules/fab/pp8_supplement/fcstd/suppl_straight_44mm_crossing_surface_260430.FCStd

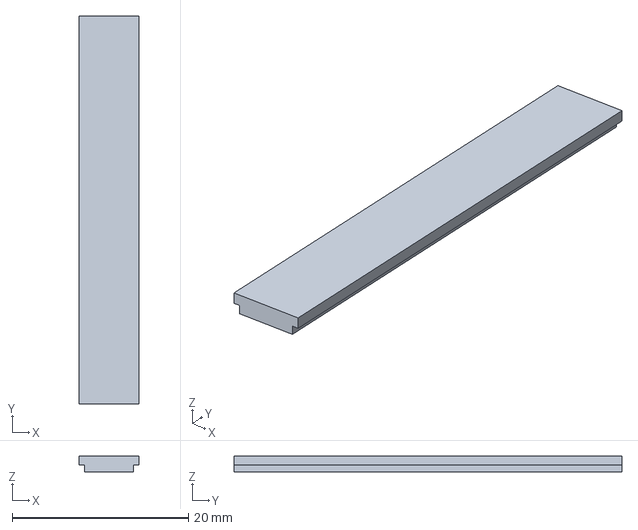
[picture p131: CAD file, 2026-04-30]
fab/pp8_supplement/fcstd/suppl_straight_44mm_crossing_surface_260430.FCStd
6.80 x 44.0 x 1.80 mm
