khartinger/RCC5V_3d-printable-parts-for-n-scale-modules/fab/pp4_track_ballast/fcstd/Gerade_Schotter_9104_260327.FCStd

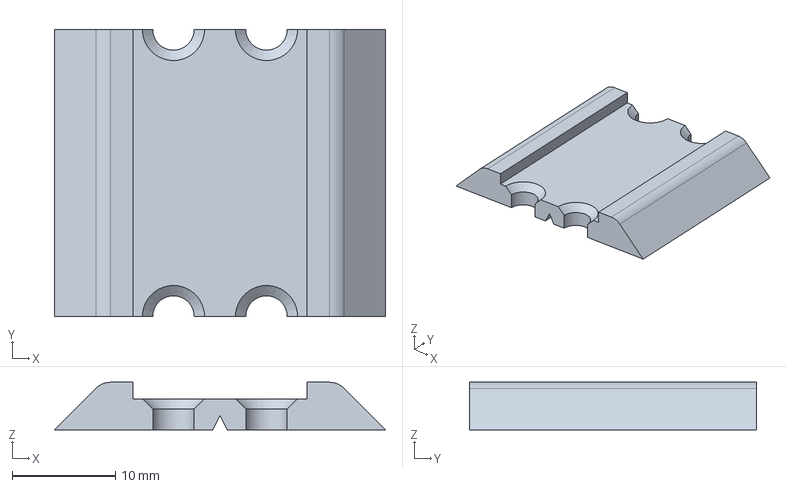
[picture p133: CAD file, 2026-04-10]
fab/pp4_track_ballast/fcstd/Gerade_Schotter_9104_260327.FCStd
32.0 x 27.8 x 4.60 mm
