khartinger/RCC5V_3d-printable-parts-for-n-scale-modules/fab/pp5_embankment/fcstd/Bogen_Damm_R2_15_9127_260311.FCStd

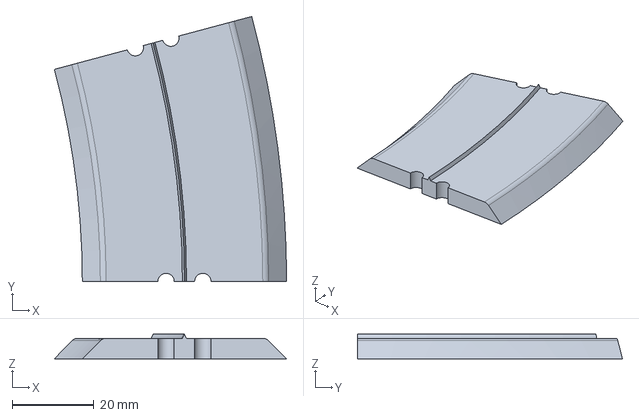
[picture p134: CAD file, 2026-04-10]
fab/pp5_embankment/fcstd/Bogen_Damm_R2_15_9127_260311.FCStd
56.8 x 64.9 x 6.00 mm
