khartinger/RCC5V_3d-printable-parts-for-n-scale-modules/fab/pp3_block_panel/fcstd/Blockpanel_Uncoupler_Text_260322.FCStd

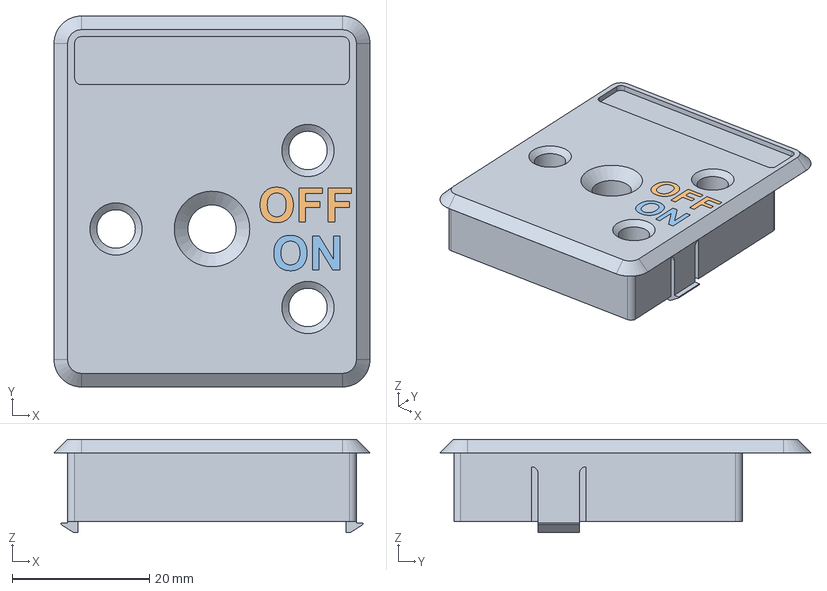
[picture p138: CAD file, 2026-04-05]
fab/pp3_block_panel/fcstd/Blockpanel_Uncoupler_Text_260322.FCStd
46.0 x 54.0 x 13.6 mm
KörperBlock
ExtrudeOFF
ExtrudeON
