khartinger/RCC5V_3d-printable-parts-for-n-scale-modules/fab/pp4_track_ballast/fcstd/Bogen_Schotter_R4_15_9136_260327.FCStd

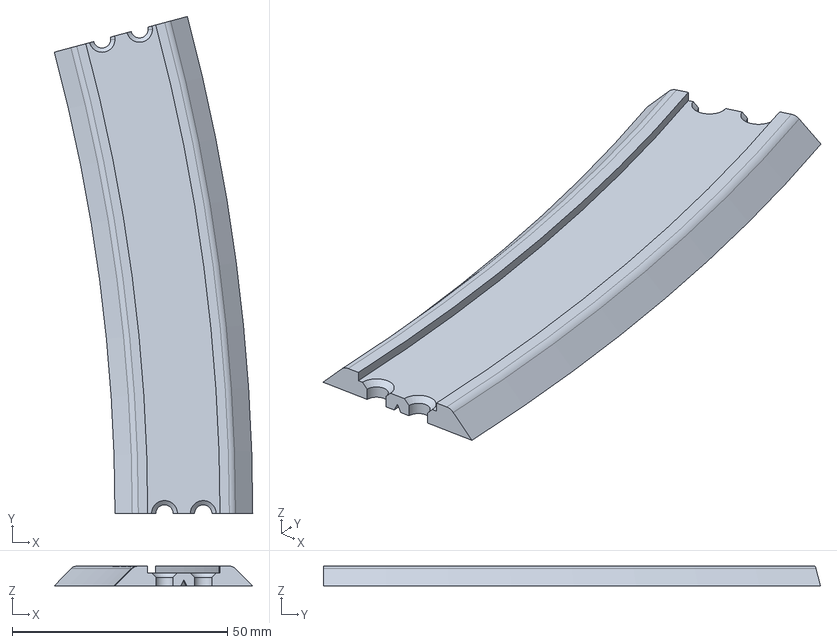
[picture p139: CAD file, 2026-04-10]
fab/pp4_track_ballast/fcstd/Bogen_Schotter_R4_15_9136_260327.FCStd
46.1 x 115.4 x 4.60 mm
