khartinger/RCC5V_3d-printable-parts-for-n-scale-modules/fab/pp5_embankment/fcstd/Gerade_Damm_9102_260311.FCStd

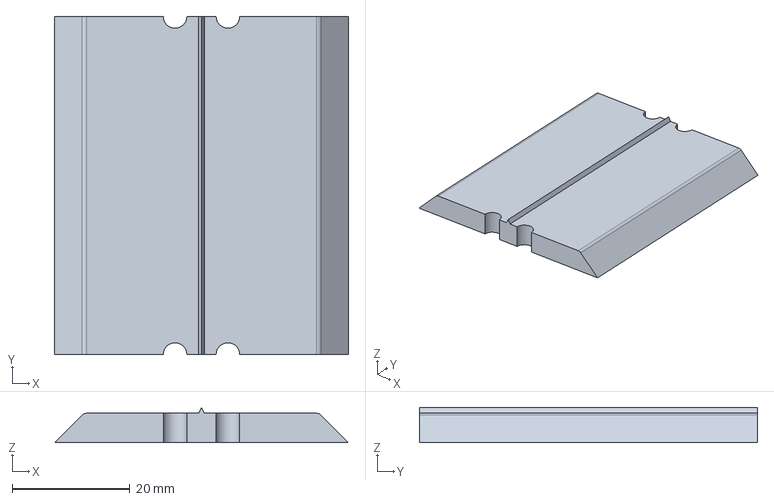
[picture p140: CAD file, 2026-04-10]
fab/pp5_embankment/fcstd/Gerade_Damm_9102_260311.FCStd
50.0 x 57.5 x 6.00 mm
