khartinger/RCC5V_3d-printable-parts-for-n-scale-modules/fab/pp8_supplement/fcstd/suppl_straight_E12_74mm_crossing_260430.FCStd

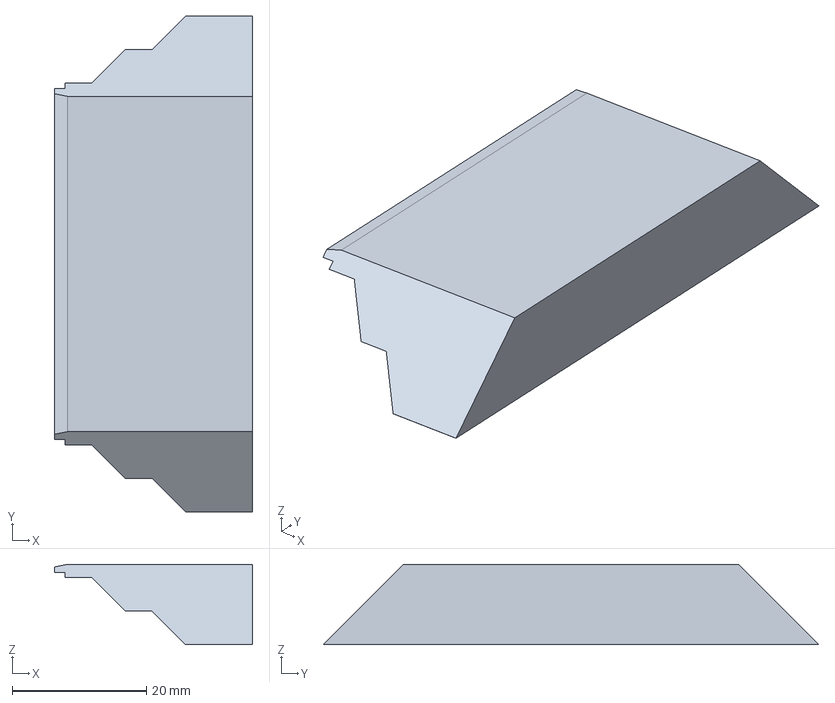
[picture p141: CAD file, 2026-04-30]
fab/pp8_supplement/fcstd/suppl_straight_E12_74mm_crossing_260430.FCStd
29.6 x 74.0 x 12.0 mm
