khartinger/RCC5V_3d-printable-parts-for-n-scale-modules/fab/pp5_embankment/fcstd/Gerade_Damm_9104_-10mm_260317.FCStd

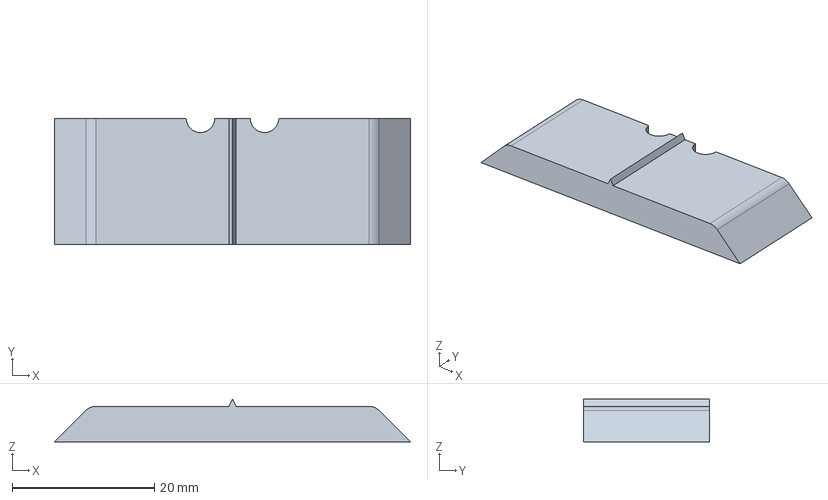
[picture p142: CAD file, 2026-04-10]
fab/pp5_embankment/fcstd/Gerade_Damm_9104_-10mm_260317.FCStd
50.0 x 17.8 x 6.00 mm
