khartinger/RCC5V_3d-printable-parts-for-n-scale-modules/fab/pp8_supplement/fcstd/suppl_straight_E8_50mm_260429.FCStd

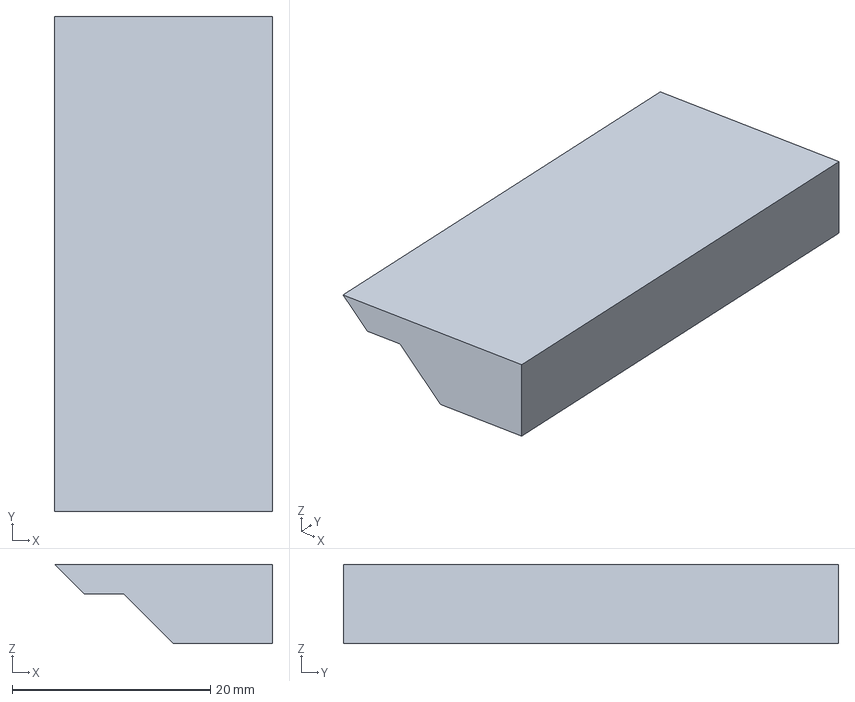
[picture p143: CAD file, 2026-04-30]
fab/pp8_supplement/fcstd/suppl_straight_E8_50mm_260429.FCStd
22.0 x 50.0 x 8.00 mm
