khartinger/RCC5V_3d-printable-parts-for-n-scale-modules/fab/pp2_baseboard_frame/fcstd/Rahmen_Front_W_Oled_34_240mm_260401.FCStd

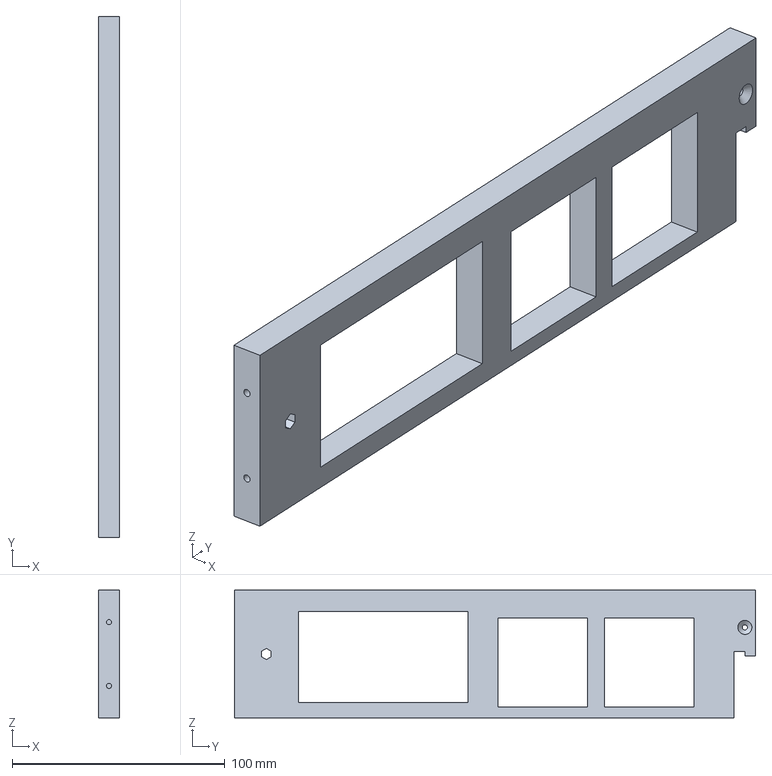
[picture p145: CAD file, 2026-04-05]
fab/pp2_baseboard_frame/fcstd/Rahmen_Front_W_Oled_34_240mm_260401.FCStd
10.0 x 245.0 x 60.0 mm
