khartinger/RCC5V_3d-printable-parts-for-n-scale-modules/fab/pp8_supplement/fcstd/suppl_straight_E10_111mm_260429.FCStd

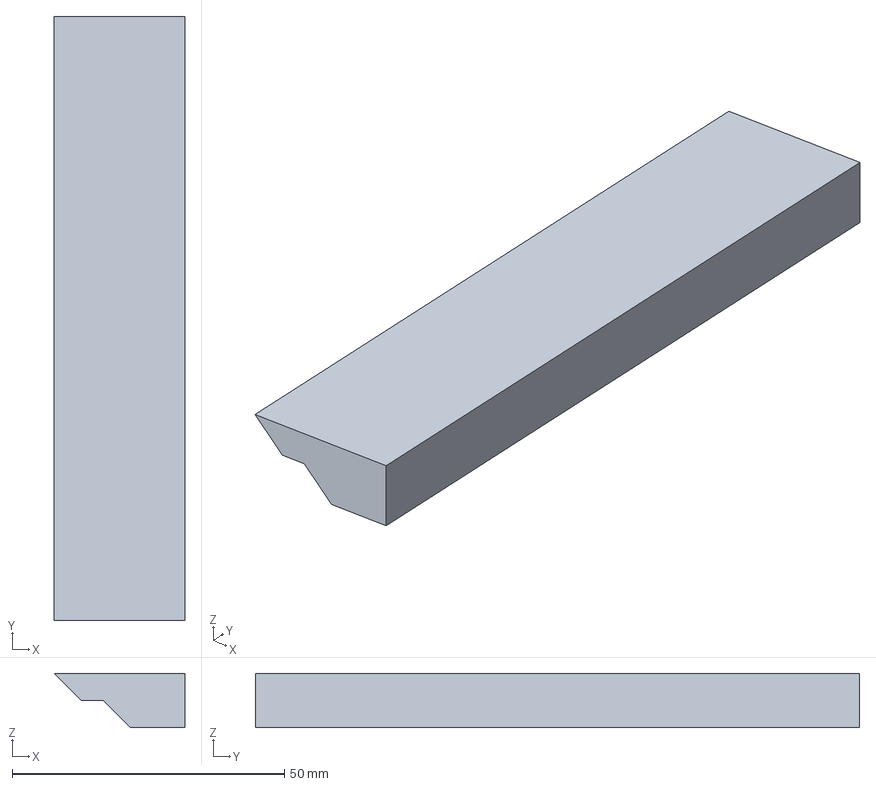
[picture p147: CAD file, 2026-04-30]
fab/pp8_supplement/fcstd/suppl_straight_E10_111mm_260429.FCStd
24.0 x 111.0 x 10.0 mm
