khartinger/RCC5V_3d-printable-parts-for-n-scale-modules/fab/pp4_track_ballast/fcstd/Bogen_Schotter_R3_9.978_9131_260327.FCStd

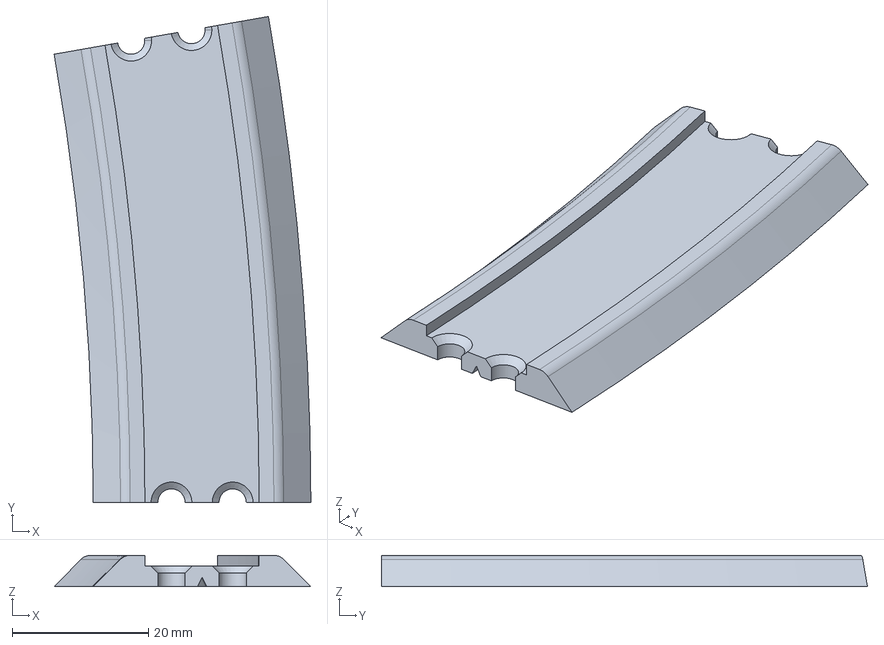
[picture p149: CAD file, 2026-04-10]
fab/pp4_track_ballast/fcstd/Bogen_Schotter_R3_9.978_9131_260327.FCStd
37.8 x 71.5 x 4.60 mm
