khartinger/RCC5V_3d-printable-parts-for-n-scale-modules/fab/pp5_embankment/fcstd/Gerade_Damm_9104_adWeiche_260314.FCStd

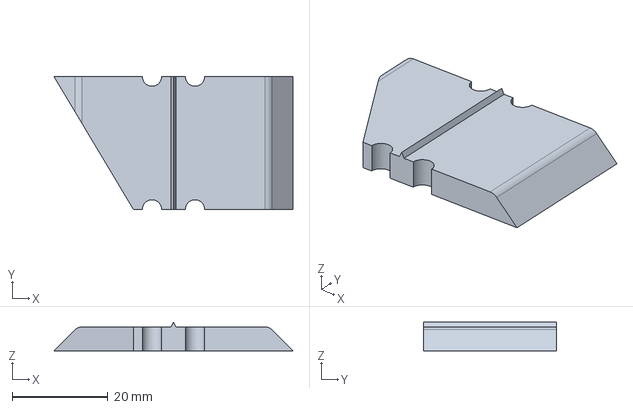
[picture p150: CAD file, 2026-04-10]
fab/pp5_embankment/fcstd/Gerade_Damm_9104_adWeiche_260314.FCStd
50.0 x 27.8 x 6.00 mm
