khartinger/RCC5V_3d-printable-parts-for-n-scale-modules/fab/pp9_projects/ReflectiveOptocoupler/fcstd/Opto_Beilage_2.2mm_260528.FCStd

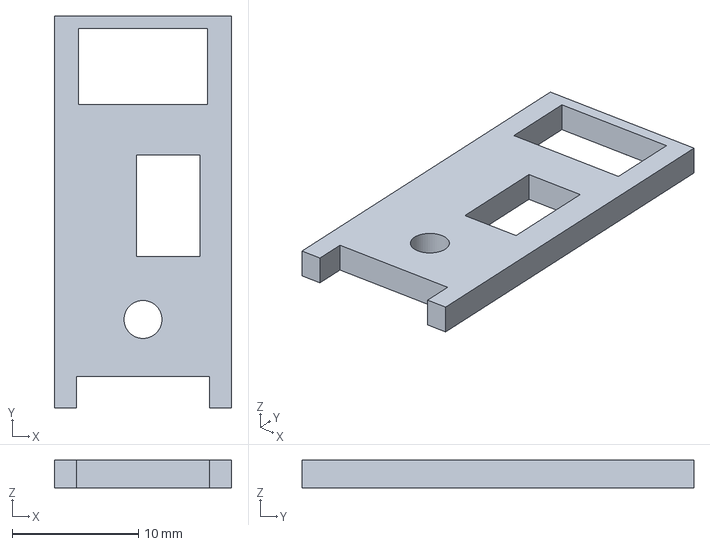
[picture p151: CAD file, 2026-06-02]
fab/pp9_projects/ReflectiveOptocoupler/fcstd/Opto_Beilage_2.2mm_260528.FCStd
14.0 x 31.0 x 2.20 mm
