khartinger/RCC5V_3d-printable-parts-for-n-scale-modules/fab/pp2_baseboard_frame/fcstd/Rahmen_Distanzplatte_2.0mm_260404.FCStd

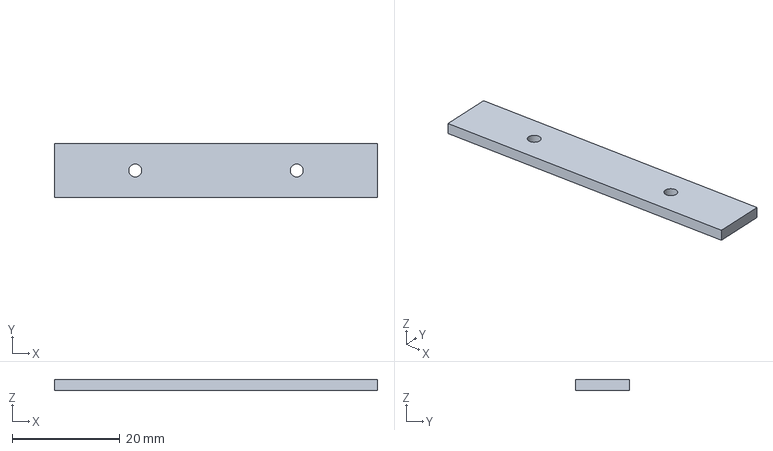
[picture p154: CAD file, 2026-04-05]
fab/pp2_baseboard_frame/fcstd/Rahmen_Distanzplatte_2.0mm_260404.FCStd
60.0 x 10.0 x 2.00 mm
