khartinger/RCC5V_3d-printable-parts-for-n-scale-modules/fab/pp4_track_ballast/fcstd/Gerade_Schotter_9110_260327.FCStd

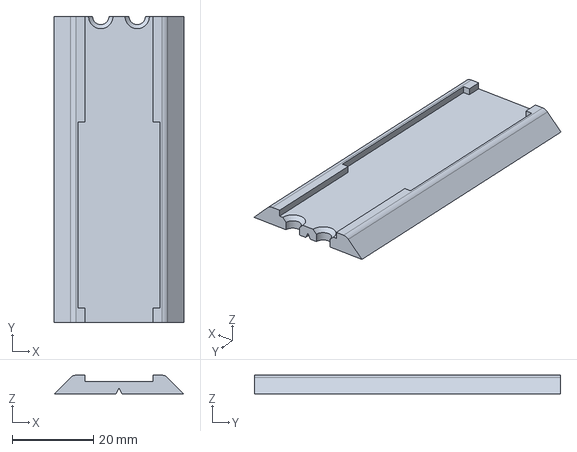
[picture p155: CAD file, 2026-04-10]
fab/pp4_track_ballast/fcstd/Gerade_Schotter_9110_260327.FCStd
32.0 x 75.6 x 4.60 mm
