khartinger/RCC5V_3d-printable-parts-for-n-scale-modules/fab/pp5_embankment/fcstd/Bogen_Damm_R3_9.978_9131_260311.FCStd

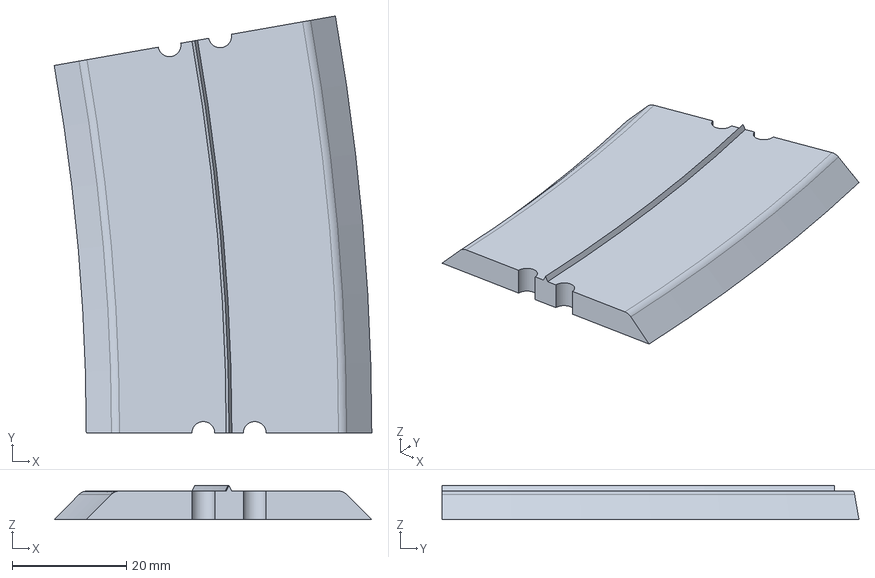
[picture p156: CAD file, 2026-04-10]
fab/pp5_embankment/fcstd/Bogen_Damm_R3_9.978_9131_260311.FCStd
55.6 x 73.0 x 6.00 mm
