khartinger/RCC5V_3d-printable-parts-for-n-scale-modules/fab/pp5_embankment/fcstd/Bogen_Damm_R4_15_9136_260311.FCStd

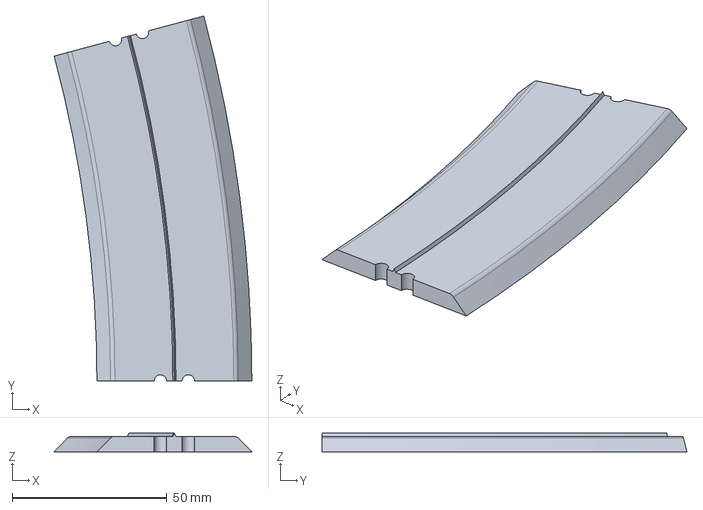
[picture p158: CAD file, 2026-04-10]
fab/pp5_embankment/fcstd/Bogen_Damm_R4_15_9136_260311.FCStd
63.8 x 117.8 x 6.00 mm
